vollbert/artix-dc-scm/Documentation/Pasted image 20260325133813.png

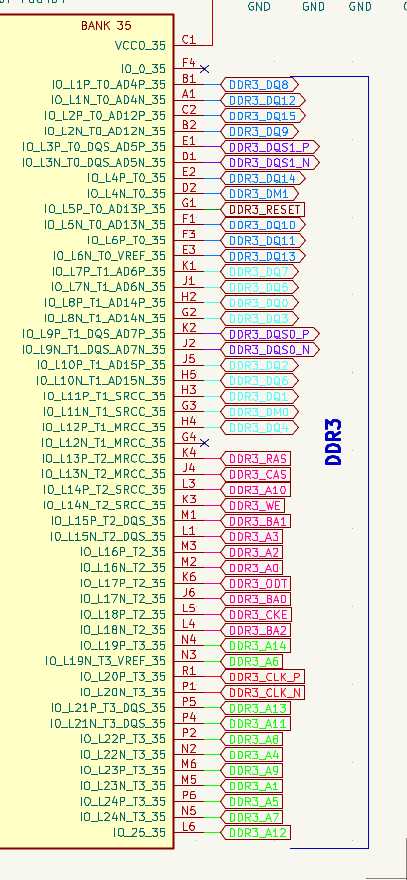
Documentation/Pasted image 20260325133813.png
