vollbert/artix-dc-scm/Documentation/Pasted image 20260326165011.png

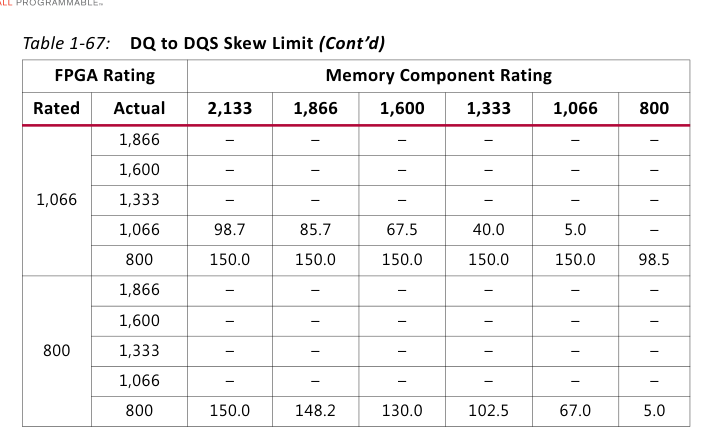
Documentation/Pasted image 20260326165011.png
