vollbert/artix-dc-scm/Documentation/Pasted image 20260402192206.png

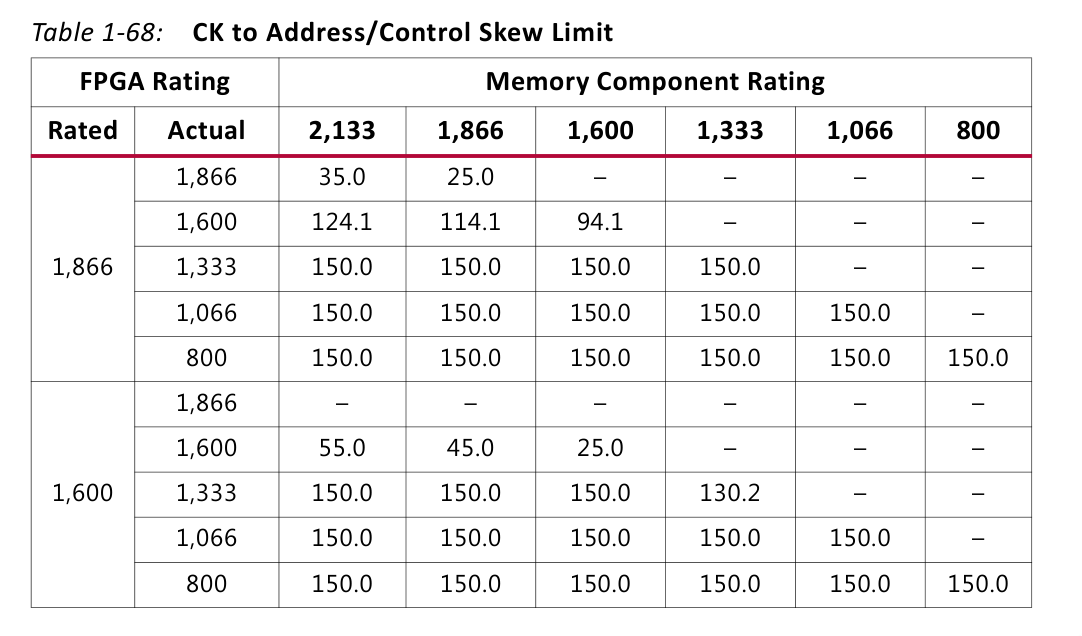
Documentation/Pasted image 20260402192206.png
