vollbert/artix-dc-scm/Documentation/Pasted image 20260403101223.png

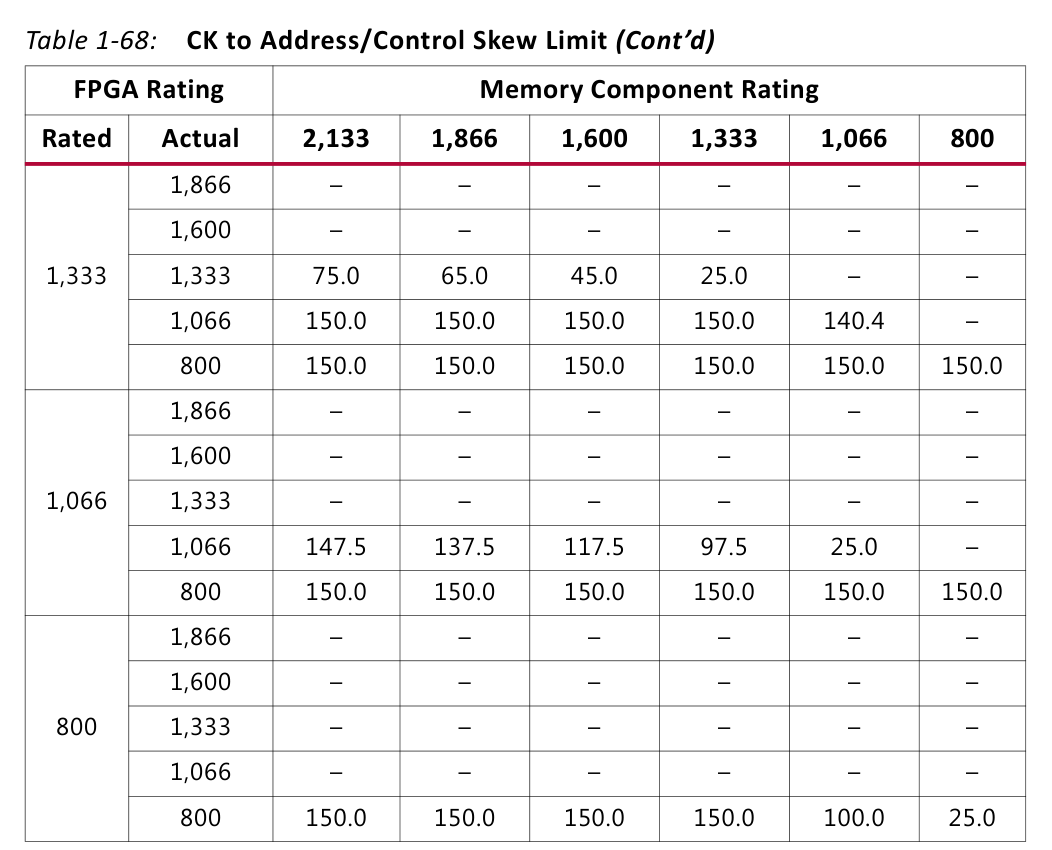
Documentation/Pasted image 20260403101223.png
