vollbert/artix-dc-scm/artix-dc-scm.kicad_sch

## KiCad design artix-dc-scm.kicad_sch (2026-04-19)

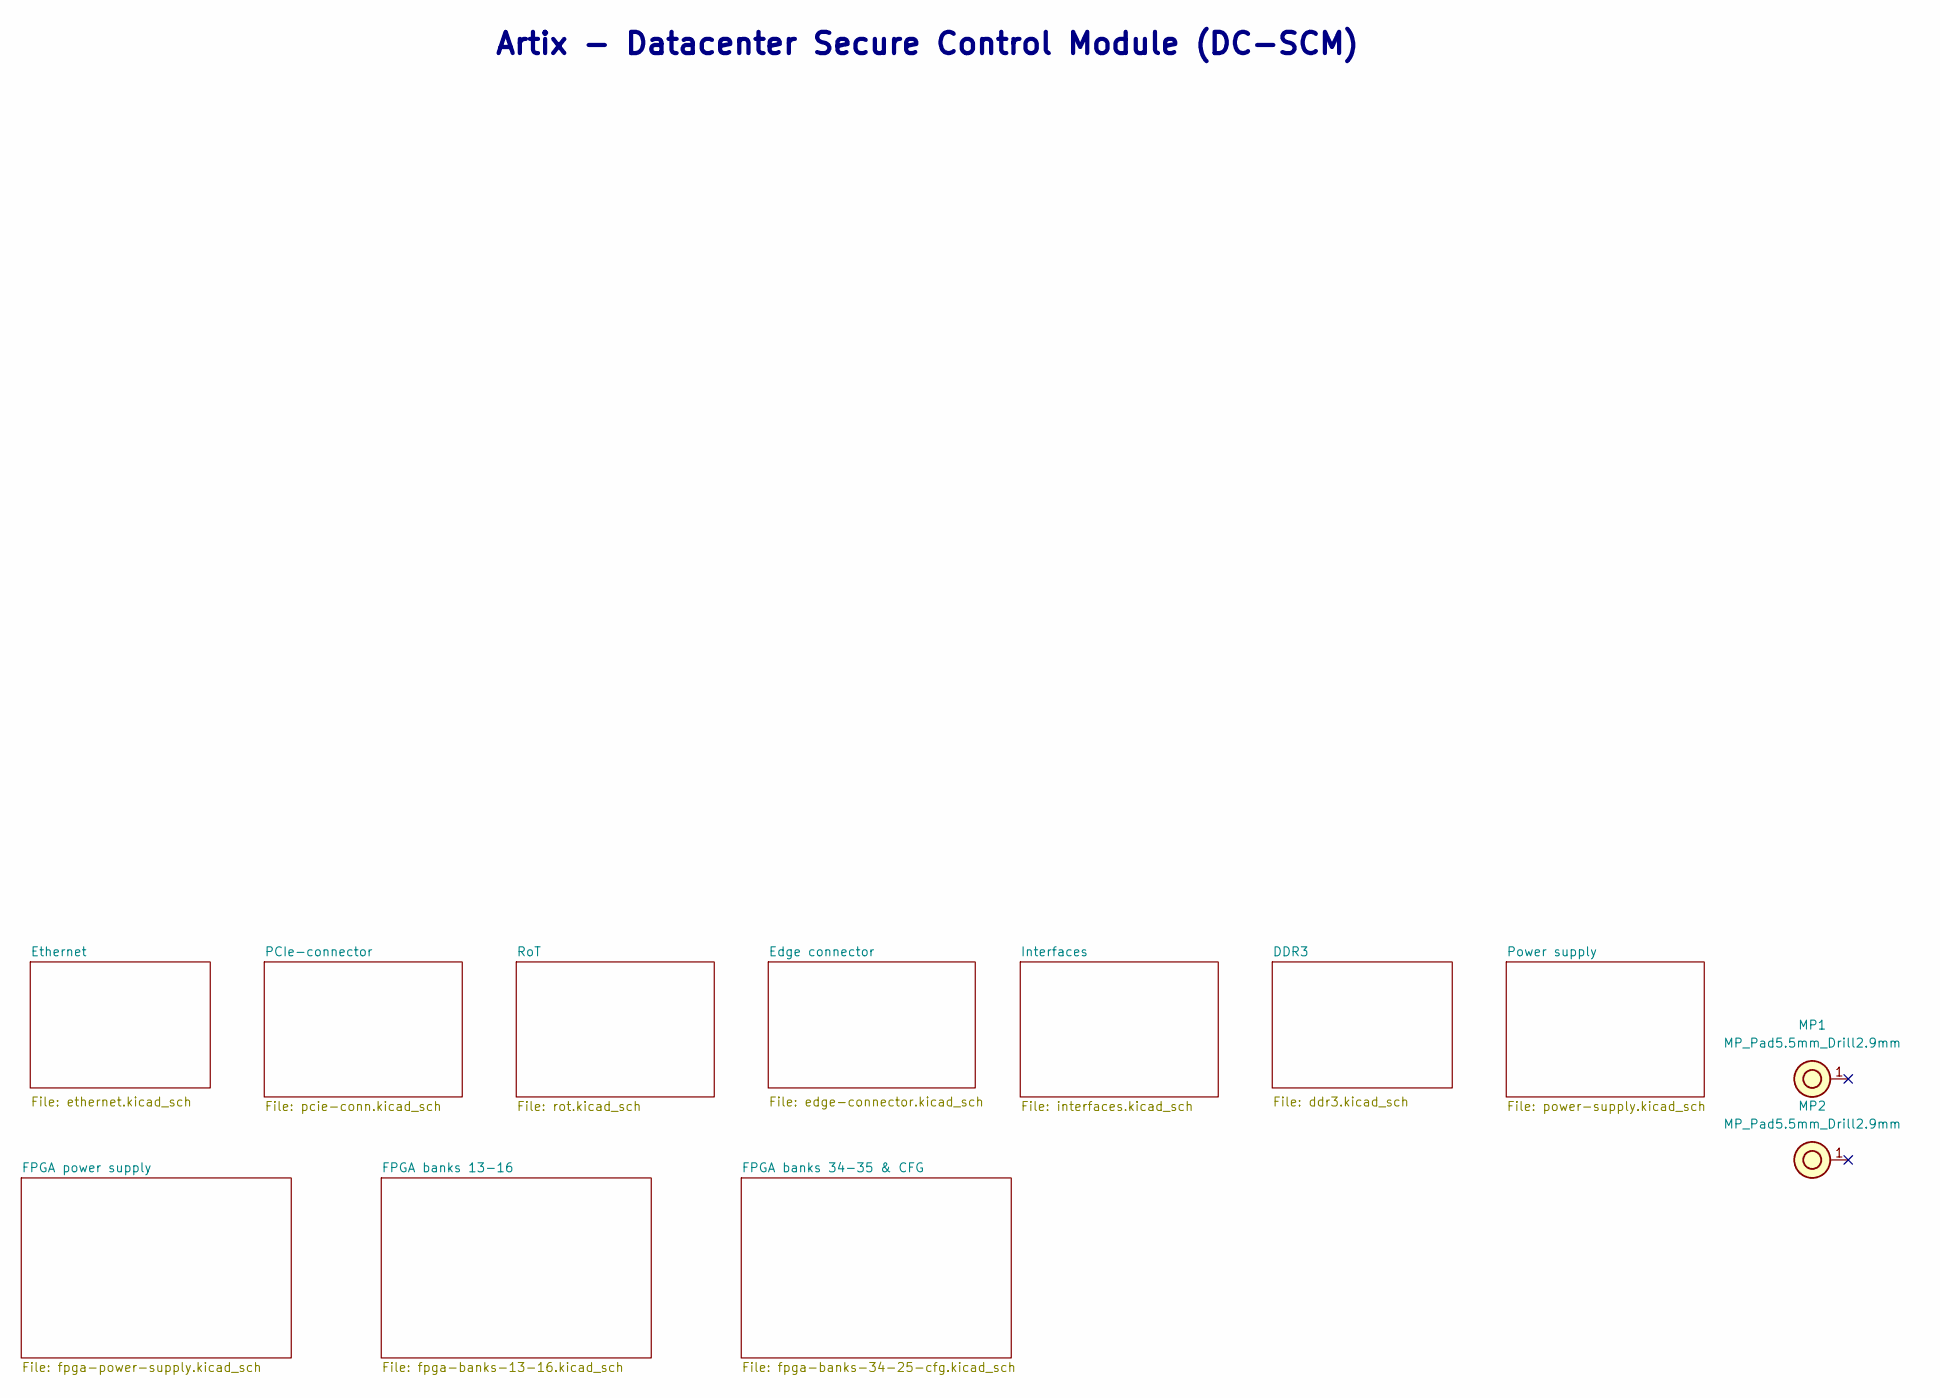
[picture p16: schematic artix-dc-scm.kicad_sch]

Parts:
MP1, MP2: MP_Pad5.5mm_Drill2.9mm

Notes on the sheet:
Artix - Datacenter Secure Control Module (DC-SCM)
