vollbert/artix-dc-scm/ddr3.kicad_sch

## KiCad design ddr3.kicad_sch (2026-04-19)

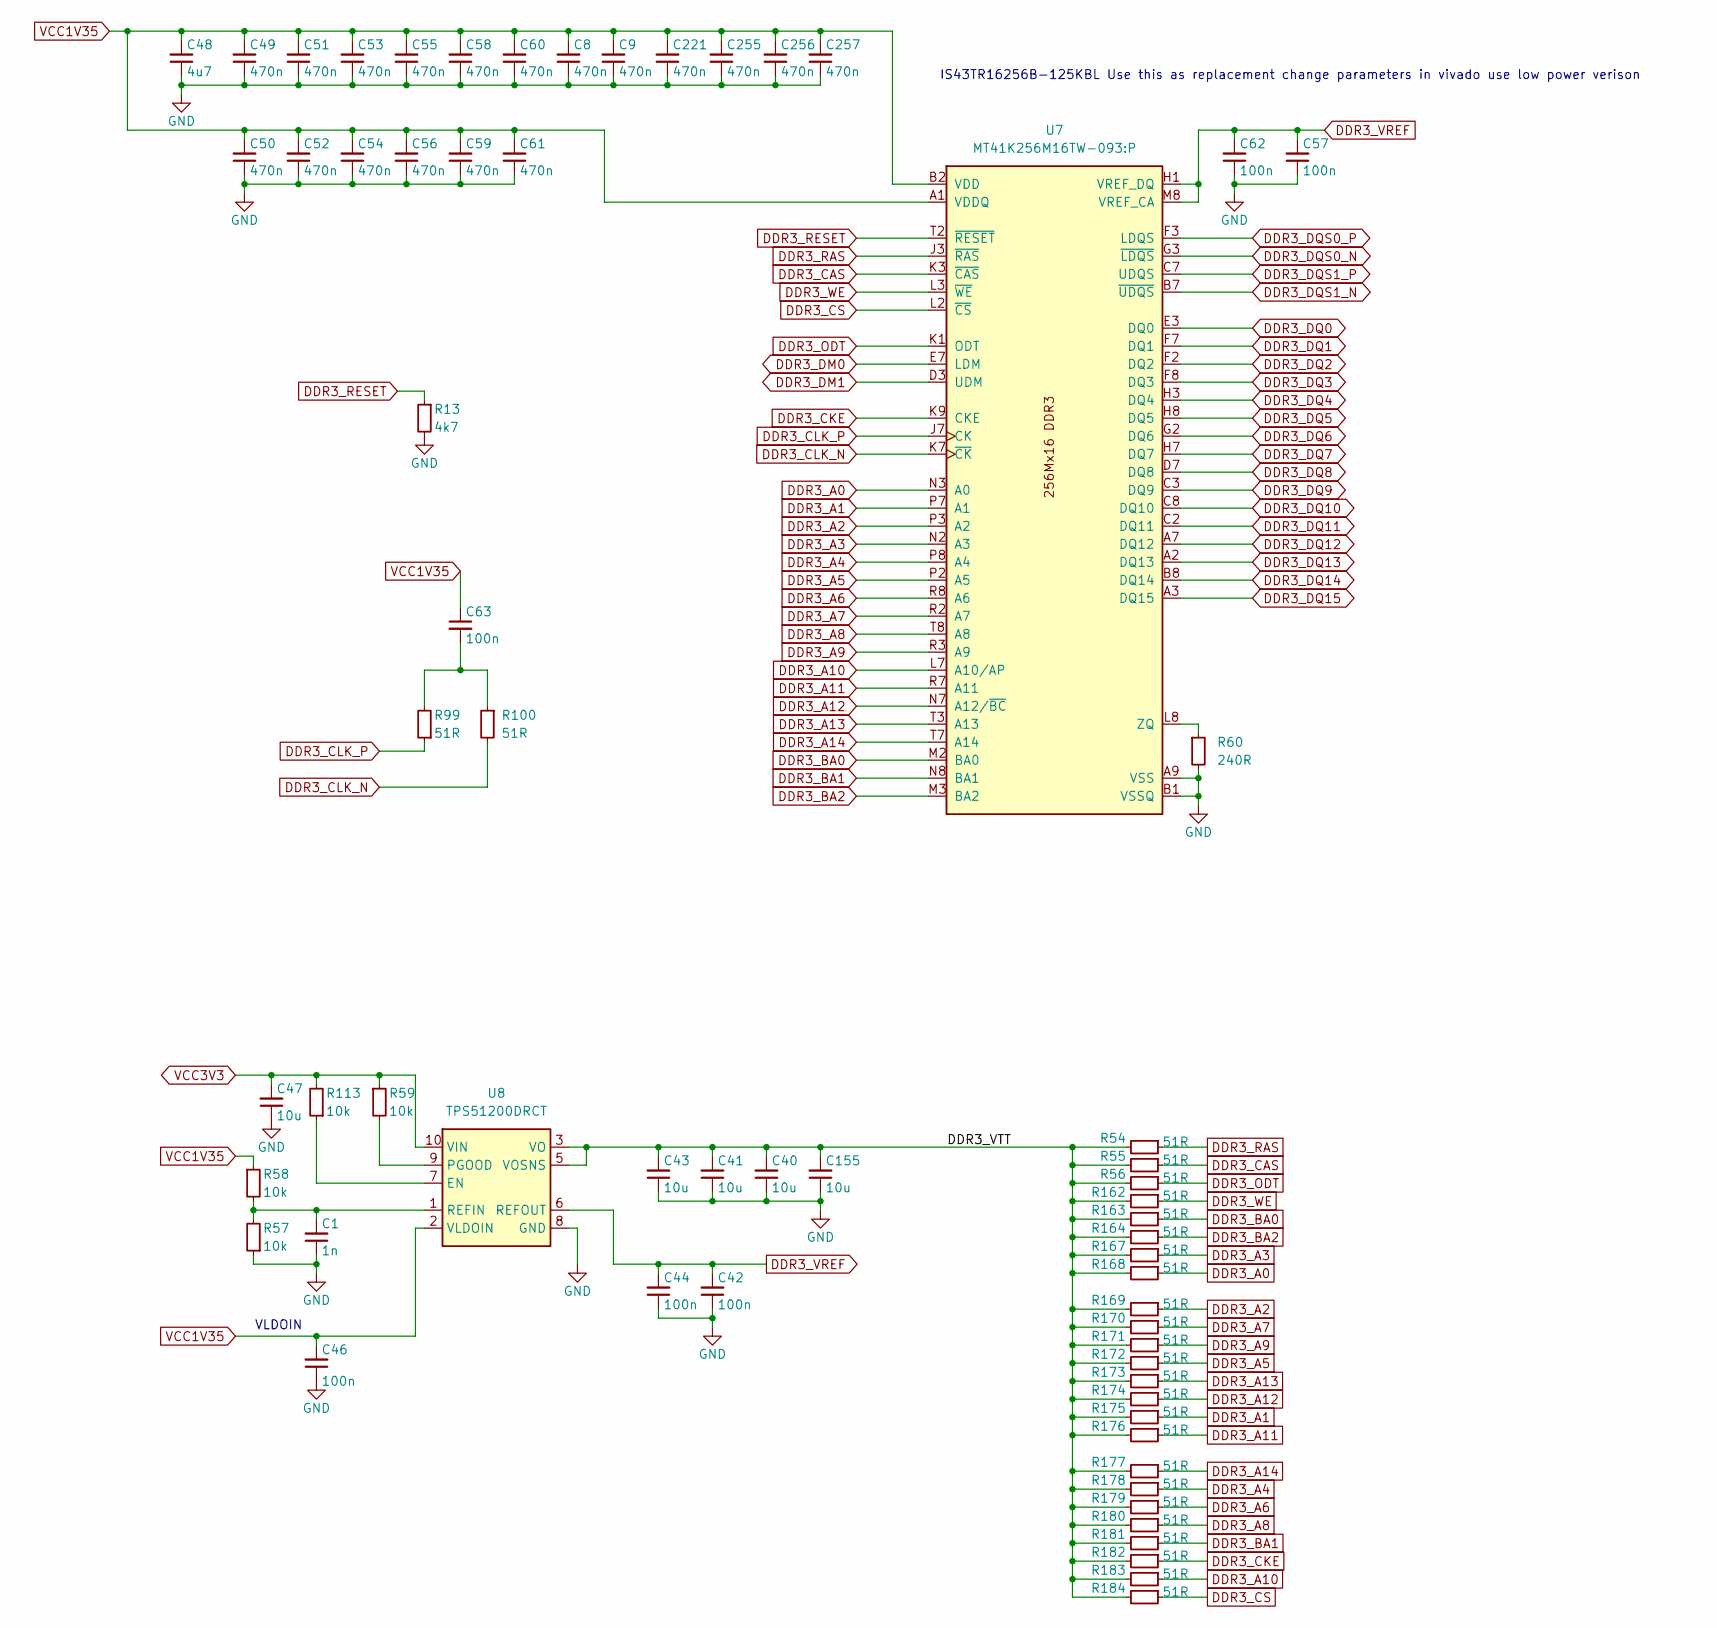
[picture p17: schematic ddr3.kicad_sch]

Parts:
C1: C_1n_0402; C_0402_1005Metric; Voltage 50V; MPN GRM1555C1H102JA01D
C8, C9, C49, C50, C51, C52, C53, C54, C55, C56, C58, C59, C60, C61, C221, C255, C256, C257: C_470n_0402; C_0402_1005Metric; MPN GXT155C80J474KE01D
C40, C41, C43, C47, C155: C_10u_0402; C_0402_1005Metric; MPN CC0402MRX5R5BB106
C42, C44, C46, C57, C62, C63: C_100n_6V3_0402; C_0402_1005Metric; MPN 0402X104K6R3CT
C48: C_4u7_0402; C_0402_1005Metric; MPN GRM155R61A475MEAAD
R13: R_4k7_0402; R_0402_1005Metric; Tolerance 1%; MPN RC0402FR-7D4K7L
R54, R55, R56, R99, R100, R162, R163, R164, R167, R168, R169, R170, R171, R172, R173, R174, R175, R176, R177, R178, R179, R180, R181, R182, R183, R184: R_51R_0402; R_0402_1005Metric; Tolerance 1%; MPN CR0402-FX-51R0GLF
R57, R58, R59, R113: R_10k_0402; R_0402_1005Metric; Tolerance 1%; MPN CR0402AFX-1002GAS
R60: R_240R_0402; R_0402_1005Metric; Tolerance 1%; MPN CR0402-FX-2400GLF
U7: MT41K256M16TW-093:P; BGA96C80P9X16_800X1400X120; MPN MT41K256M16TW-093:P
U8: TPS51200DRCT; VSON-10-1EP_3x3mm; MPN TPS51200DRCT

Connections:
DDR3_A0: R168.1, U7.N3 (A0)
DDR3_A1: R175.1, U7.P7 (A1)
DDR3_A2: R169.1, U7.P3 (A2)
DDR3_A3: R167.1, U7.N2 (A3)
DDR3_A4: R178.1, U7.P8 (A4)
DDR3_A5: R172.1, U7.P2 (A5)
DDR3_A6: R179.1, U7.R8 (A6)
DDR3_A7: R170.1, U7.R2 (A7)
DDR3_A8: R180.1, U7.T8 (A8)
DDR3_A9: R171.1, U7.R3 (A9)
DDR3_A10: R183.1, U7.L7 (A10/AP)
DDR3_A11: R176.1, U7.R7 (A11)
DDR3_A12: R174.1, U7.N7 (A12/~BC)
DDR3_A13: R173.1, U7.T3 (A13)
DDR3_A14: R177.1, U7.T7 (A14)
DDR3_BA0: R163.1, U7.M2 (BA0)
DDR3_BA1: R181.1, U7.N8 (BA1)
DDR3_BA2: R164.1, U7.M3 (BA2)
DDR3_CAS: R55.1, U7.K3 (~CAS)
DDR3_CKE: R182.1, U7.K9 (CKE)
DDR3_CLK_N: R100.2, U7.K7 (~CK)
DDR3_CLK_P: R99.1, U7.J7 (CK)
DDR3_CS: R184.1, U7.L2 (~CS)
DDR3_DM0: U7.E7 (LDM)
DDR3_DM1: U7.D3 (UDM)
DDR3_DQ0: U7.E3 (DQ0)
DDR3_DQ1: U7.F7 (DQ1)
DDR3_DQ2: U7.F2 (DQ2)
DDR3_DQ3: U7.F8 (DQ3)
DDR3_DQ4: U7.H3 (DQ4)
DDR3_DQ5: U7.H8 (DQ5)
DDR3_DQ6: U7.G2 (DQ6)
DDR3_DQ7: U7.H7 (DQ7)
DDR3_DQ8: U7.D7 (DQ8)
DDR3_DQ9: U7.C3 (DQ9)
DDR3_DQ10: U7.C8 (DQ10)
DDR3_DQ11: U7.C2 (DQ11)
DDR3_DQ12: U7.A7 (DQ12)
DDR3_DQ13: U7.A2 (DQ13)
DDR3_DQ14: U7.B8 (DQ14)
DDR3_DQ15: U7.A3 (DQ15)
DDR3_DQS0_N: U7.G3 (~LDQS)
DDR3_DQS0_P: U7.F3 (LDQS)
DDR3_DQS1_N: U7.B7 (~UDQS)
DDR3_DQS1_P: U7.C7 (UDQS)
DDR3_ODT: R56.1, U7.K1 (ODT)
DDR3_RAS: R54.1, U7.J3 (~RAS)
DDR3_RESET: R13.1, U7.T2 (~RESET)
DDR3_VREF: C42.2, C44.2, C57.2, C62.2, U7.H1 (VREF_DQ), U7.M8 (VREF_CA), U8.6 (REFOUT)
DDR3_VTT: C40.2, C41.2, C43.2, C155.2, R54.2, R55.2, R56.2, R162.2, R163.2, R164.2, R167.2, R168.2, R169.2, R170.2, R171.2, R172.2, R173.2, R174.2, R175.2, R176.2, R177.2, R178.2, R179.2, R180.2, R181.2, R182.2, R183.2, R184.2, U8.3 (VO), U8.5 (VOSNS)
DDR3_WE: R162.1, U7.L3 (~WE)
GND: C1.1, C8.1, C9.1, C40.1, C41.1, C42.1, C43.1, C44.1, C46.1, C47.1, C48.1, C49.1, C50.1, C51.1, C52.1, C53.1, C54.1, C55.1, C56.1, C57.1, C58.1, C59.1, C60.1, C61.1, C62.1, C155.1, C221.1, C255.1, C256.1, C257.1, R13.2, R57.1, R60.2, U7.A9 (VSS), U7.B1 (VSSQ), U7.B3 (VSS), U7.B9 (VSSQ), U7.D1 (VSSQ), U7.D8 (VSSQ), U7.E1 (VSS), U7.E2 (VSSQ), U7.E8 (VSSQ), U7.F9 (VSSQ), U7.G1 (VSSQ), U7.G8 (VSS), U7.G9 (VSSQ), U7.J2 (VSS), U7.J8 (VSS), U7.M1 (VSS), U7.M9 (VSS), U7.P1 (VSS), U7.P9 (VSS), U7.T1 (VSS), U7.T9 (VSS), U8.4 (GND), U8.8 (GND), U8.11 (GND)
unnamed: C1.2, R57.2, R58.2, U8.1 (REFIN)
unnamed: C63.2, R99.2, R100.1
unnamed: R59.2, U8.9 (PGOOD)
unnamed: R60.1, U7.L8 (ZQ)
unnamed: R113.1, U8.7 (EN)
unnamed: U7.J1 (NC), U7.J9 (NC), U7.L1 (NC), U7.L9 (NC), U7.M7 (NC)
VCC1V35: C8.2, C9.2, C46.2, C48.2, C49.2, C50.2, C51.2, C52.2, C53.2, C54.2, C55.2, C56.2, C58.2, C59.2, C60.2, C61.2, C63.1, C221.2, C255.2, C256.2, C257.2, R58.1, U7.A1 (VDDQ), U7.A8 (VDDQ), U7.B2 (VDD), U7.C1 (VDDQ), U7.C9 (VDDQ), U7.D2 (VDDQ), U7.D9 (VDD), U7.E9 (VDDQ), U7.F1 (VDDQ), U7.G7 (VDD), U7.H2 (VDDQ), U7.H9 (VDDQ), U7.K2 (VDD), U7.K8 (VDD), U7.N1 (VDD), U7.N9 (VDD), U7.R1 (VDD), U7.R9 (VDD), U8.2 (VLDOIN)
VCC3V3: C47.2, R59.1, R113.2, U8.10 (VIN)

Notes on the sheet:
VLDOIN
IS43TR16256B-125KBL Use this as replacement change parameters in vivado use low power verison
