vollbert/artix-dc-scm/edge-connector.kicad_sch

## KiCad design edge-connector.kicad_sch (2026-04-19)

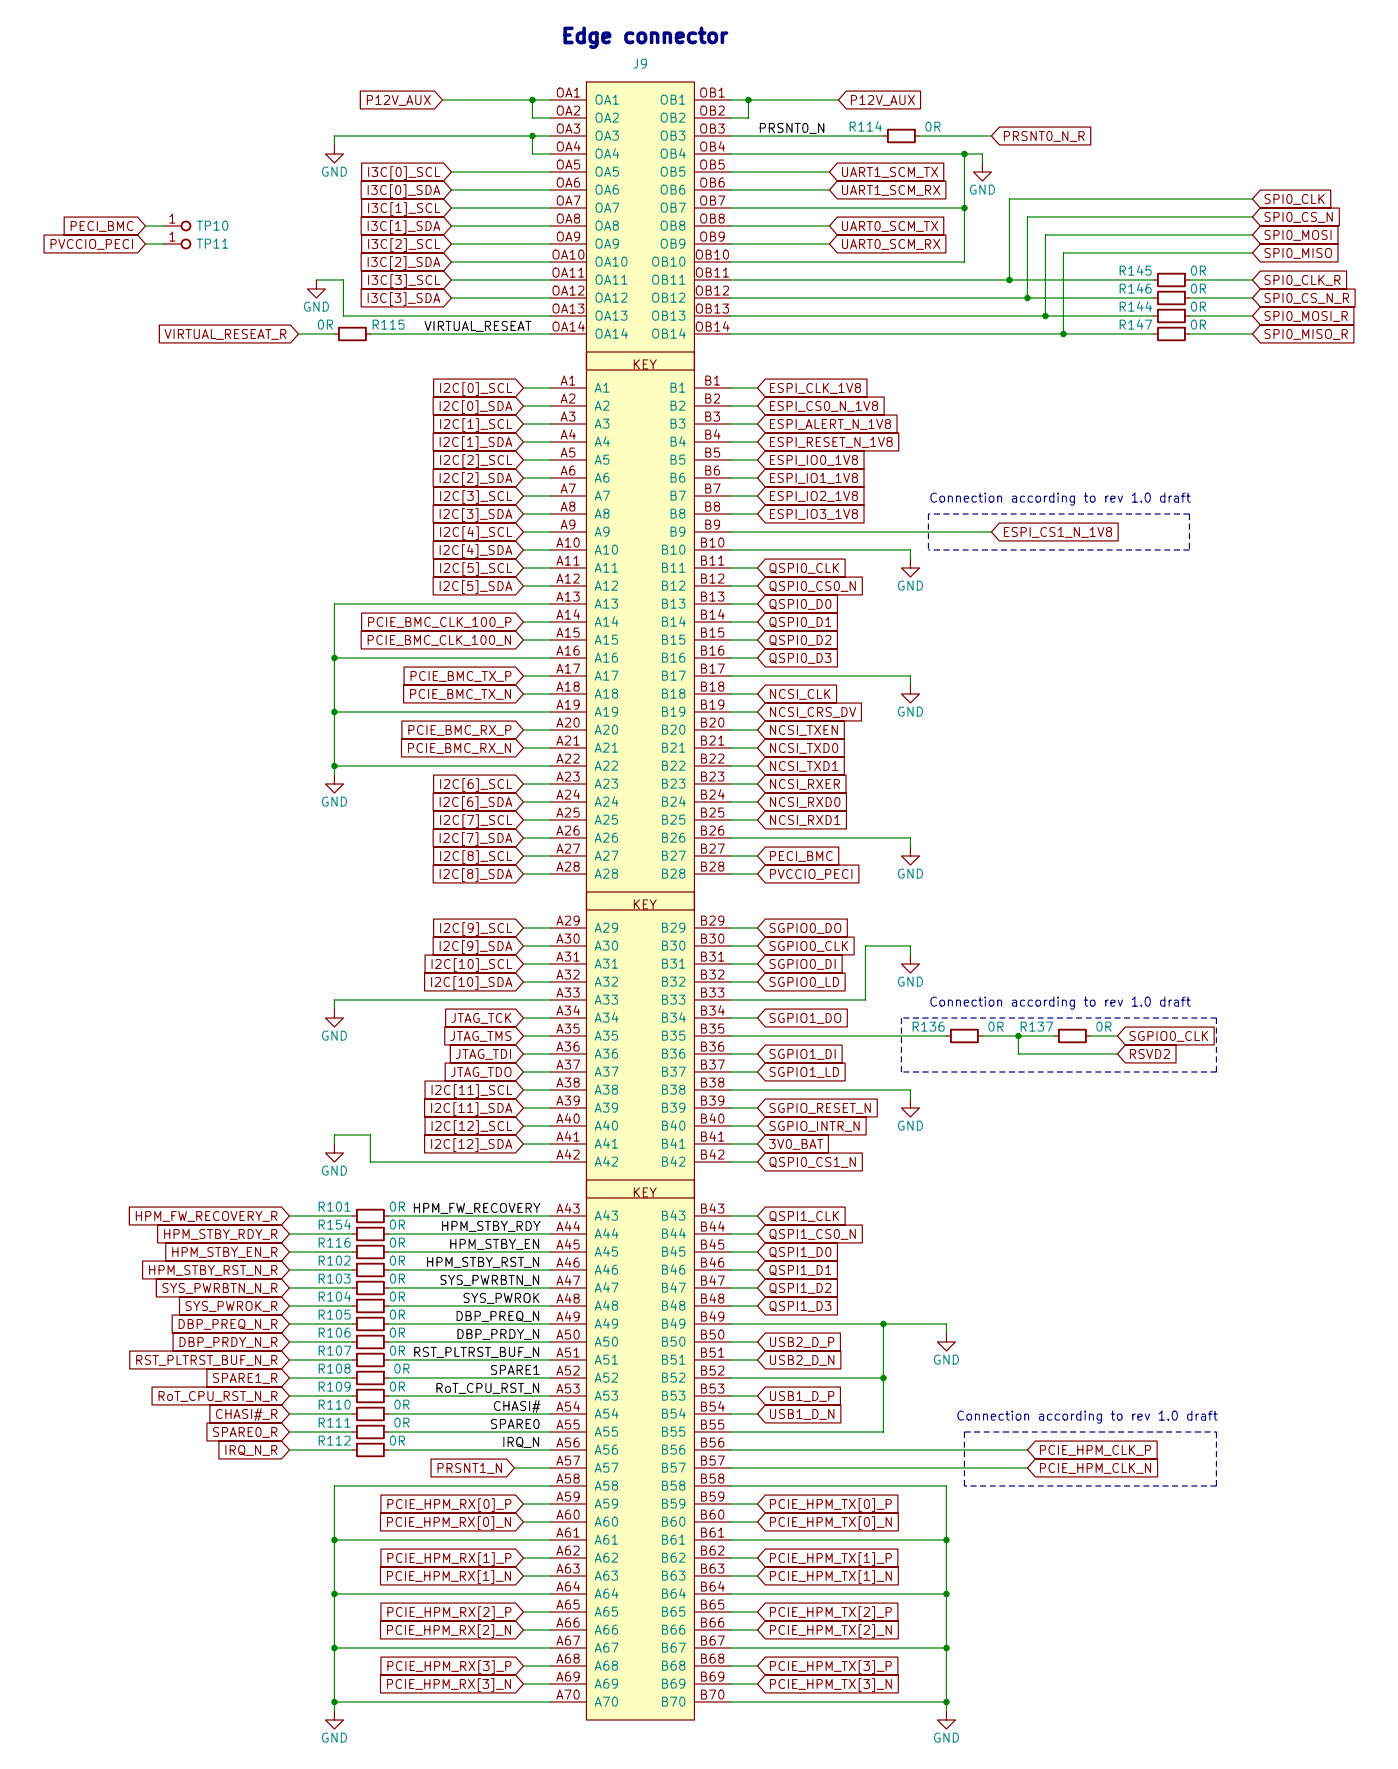
[picture p18: schematic edge-connector.kicad_sch]

Parts:
J9: SFF-TA-1002-4C+
R101, R102, R103, R104, R105, R106, R107, R108, R109, R110, R111, R112, R114, R115, R116, R136, R137, R144, R145, R146, R147, R154: R_0R_0402; R_0402_1005Metric; MPN RC0402JR-7D0RL
TP10, TP11: TP_1mm_SMD; TP_SMD_1mm

Connections:
3V0_BAT: J9.B41
CHASI#: J9.A54, R110.1
CHASI#_R: R110.2
DBP_PRDY_N: J9.A50, R106.2
DBP_PRDY_N_R: R106.1
DBP_PREQ_N: J9.A49, R105.2
DBP_PREQ_N_R: R105.1
ESPI_ALERT_N_1V8: J9.B3
ESPI_CLK_1V8: J9.B1
ESPI_CS0_N_1V8: J9.B2
ESPI_CS1_N_1V8: J9.B9
ESPI_IO0_1V8: J9.B5
ESPI_IO1_1V8: J9.B6
ESPI_IO2_1V8: J9.B7
ESPI_IO3_1V8: J9.B8
ESPI_RESET_N_1V8: J9.B4
GND: J9.A13, J9.A16, J9.A19, J9.A22, J9.A33, J9.A42, J9.A58, J9.A61, J9.A64, J9.A67, J9.A70, J9.B10, J9.B17, J9.B26, J9.B33, J9.B38, J9.B49, J9.B52, J9.B55, J9.B58, J9.B61, J9.B64, J9.B67, J9.B70, J9.OA3, J9.OA4, J9.OA13, J9.OB4, J9.OB7, J9.OB10
HPM_FW_RECOVERY: J9.A43, R101.2
HPM_FW_RECOVERY_R: R101.1
HPM_STBY_EN: J9.A45, R116.2
HPM_STBY_EN_R: R116.1
HPM_STBY_RDY: J9.A44, R154.2
HPM_STBY_RDY_R: R154.1
HPM_STBY_RST_N: J9.A46, R102.2
HPM_STBY_RST_N_R: R102.1
I2C[0]_SCL: J9.A1
I2C[0]_SDA: J9.A2
I2C[1]_SCL: J9.A3
I2C[1]_SDA: J9.A4
I2C[2]_SCL: J9.A5
I2C[2]_SDA: J9.A6
I2C[3]_SCL: J9.A7
I2C[3]_SDA: J9.A8
I2C[4]_SCL: J9.A9
I2C[4]_SDA: J9.A10
I2C[5]_SCL: J9.A11
I2C[5]_SDA: J9.A12
I2C[6]_SCL: J9.A23
I2C[6]_SDA: J9.A24
I2C[7]_SCL: J9.A25
I2C[7]_SDA: J9.A26
I2C[8]_SCL: J9.A27
I2C[8]_SDA: J9.A28
I2C[9]_SCL: J9.A29
I2C[9]_SDA: J9.A30
I2C[10]_SCL: J9.A31
I2C[10]_SDA: J9.A32
I2C[11]_SCL: J9.A38
I2C[11]_SDA: J9.A39
I2C[12]_SCL: J9.A40
I2C[12]_SDA: J9.A41
I3C[0]_SCL: J9.OA5
I3C[0]_SDA: J9.OA6
I3C[1]_SCL: J9.OA7
I3C[1]_SDA: J9.OA8
I3C[2]_SCL: J9.OA9
I3C[2]_SDA: J9.OA10
I3C[3]_SCL: J9.OA11
I3C[3]_SDA: J9.OA12
IRQ_N: J9.A56, R112.2
IRQ_N_R: R112.1
JTAG_TCK: J9.A34
JTAG_TDI: J9.A36
JTAG_TDO: J9.A37
JTAG_TMS: J9.A35
NCSI_CLK: J9.B18
NCSI_CRS_DV: J9.B19
NCSI_RXD0: J9.B24
NCSI_RXD1: J9.B25
NCSI_RXER: J9.B23
NCSI_TXD0: J9.B21
NCSI_TXD1: J9.B22
NCSI_TXEN: J9.B20
unnamed: J9.B35, R136.1
P12V_AUX: J9.OA1, J9.OA2, J9.OB1, J9.OB2
PCIE_BMC_CLK_100_N: J9.A15
PCIE_BMC_CLK_100_P: J9.A14
PCIE_BMC_RX_N: J9.A21
PCIE_BMC_RX_P: J9.A20
PCIE_BMC_TX_N: J9.A18
PCIE_BMC_TX_P: J9.A17
PCIE_HPM_CLK_N: J9.B57
PCIE_HPM_CLK_P: J9.B56
PCIE_HPM_RX[0]_N: J9.A60
PCIE_HPM_RX[0]_P: J9.A59
PCIE_HPM_RX[1]_N: J9.A63
PCIE_HPM_RX[1]_P: J9.A62
PCIE_HPM_RX[2]_N: J9.A66
PCIE_HPM_RX[2]_P: J9.A65
PCIE_HPM_RX[3]_N: J9.A69
PCIE_HPM_RX[3]_P: J9.A68
PCIE_HPM_TX[0]_N: J9.B60
PCIE_HPM_TX[0]_P: J9.B59
PCIE_HPM_TX[1]_N: J9.B63
PCIE_HPM_TX[1]_P: J9.B62
PCIE_HPM_TX[2]_N: J9.B66
PCIE_HPM_TX[2]_P: J9.B65
PCIE_HPM_TX[3]_N: J9.B69
PCIE_HPM_TX[3]_P: J9.B68
PECI_BMC: J9.B27, TP10.1
PRSNT0_N: J9.OB3, R114.2
PRSNT0_N_R: R114.1
PRSNT1_N: J9.A57
PVCCIO_PECI: J9.B28, TP11.1
QSPI0_CLK: J9.B11
QSPI0_CS0_N: J9.B12
QSPI0_CS1_N: J9.B42
QSPI0_D0: J9.B13
QSPI0_D1: J9.B14
QSPI0_D2: J9.B15
QSPI0_D3: J9.B16
QSPI1_CLK: J9.B43
QSPI1_CS0_N: J9.B44
QSPI1_D0: J9.B45
QSPI1_D1: J9.B46
QSPI1_D2: J9.B47
QSPI1_D3: J9.B48
RST_PLTRST_BUF_N: J9.A51, R107.2
RST_PLTRST_BUF_N_R: R107.1
RSVD2: R136.2, R137.1
RoT_CPU_RST_N: J9.A53, R109.2
RoT_CPU_RST_N_R: R109.1
SGPIO0_CLK: J9.B30, R137.2
SGPIO0_DI: J9.B31
SGPIO0_DO: J9.B29
SGPIO0_LD: J9.B32
SGPIO1_DI: J9.B36
SGPIO1_DO: J9.B34
SGPIO1_LD: J9.B37
SGPIO_INTR_N: J9.B40
SGPIO_RESET_N: J9.B39
SPARE0: J9.A55, R111.1
SPARE0_R: R111.2
SPARE1: J9.A52, R108.1
SPARE1_R: R108.2
SPI0_CLK: J9.OB11, R145.2
SPI0_CLK_R: R145.1
SPI0_CS_N: J9.OB12, R146.2
SPI0_CS_N_R: R146.1
SPI0_MISO: J9.OB14, R147.2
SPI0_MISO_R: R147.1
SPI0_MOSI: J9.OB13, R144.2
SPI0_MOSI_R: R144.1
SYS_PWRBTN_N: J9.A47, R103.2
SYS_PWRBTN_N_R: R103.1
SYS_PWROK: J9.A48, R104.2
SYS_PWROK_R: R104.1
UART0_SCM_RX: J9.OB9
UART0_SCM_TX: J9.OB8
UART1_SCM_RX: J9.OB6
UART1_SCM_TX: J9.OB5
USB1_D_N: J9.B54
USB1_D_P: J9.B53
USB2_D_N: J9.B51
USB2_D_P: J9.B50
VIRTUAL_RESEAT: J9.OA14, R115.2
VIRTUAL_RESEAT_R: R115.1

Notes on the sheet:
Edge connector
Connection according to rev 1.0 draft
