vollbert/artix-dc-scm/ethernet.kicad_sch

## KiCad design ethernet.kicad_sch (2026-04-19)

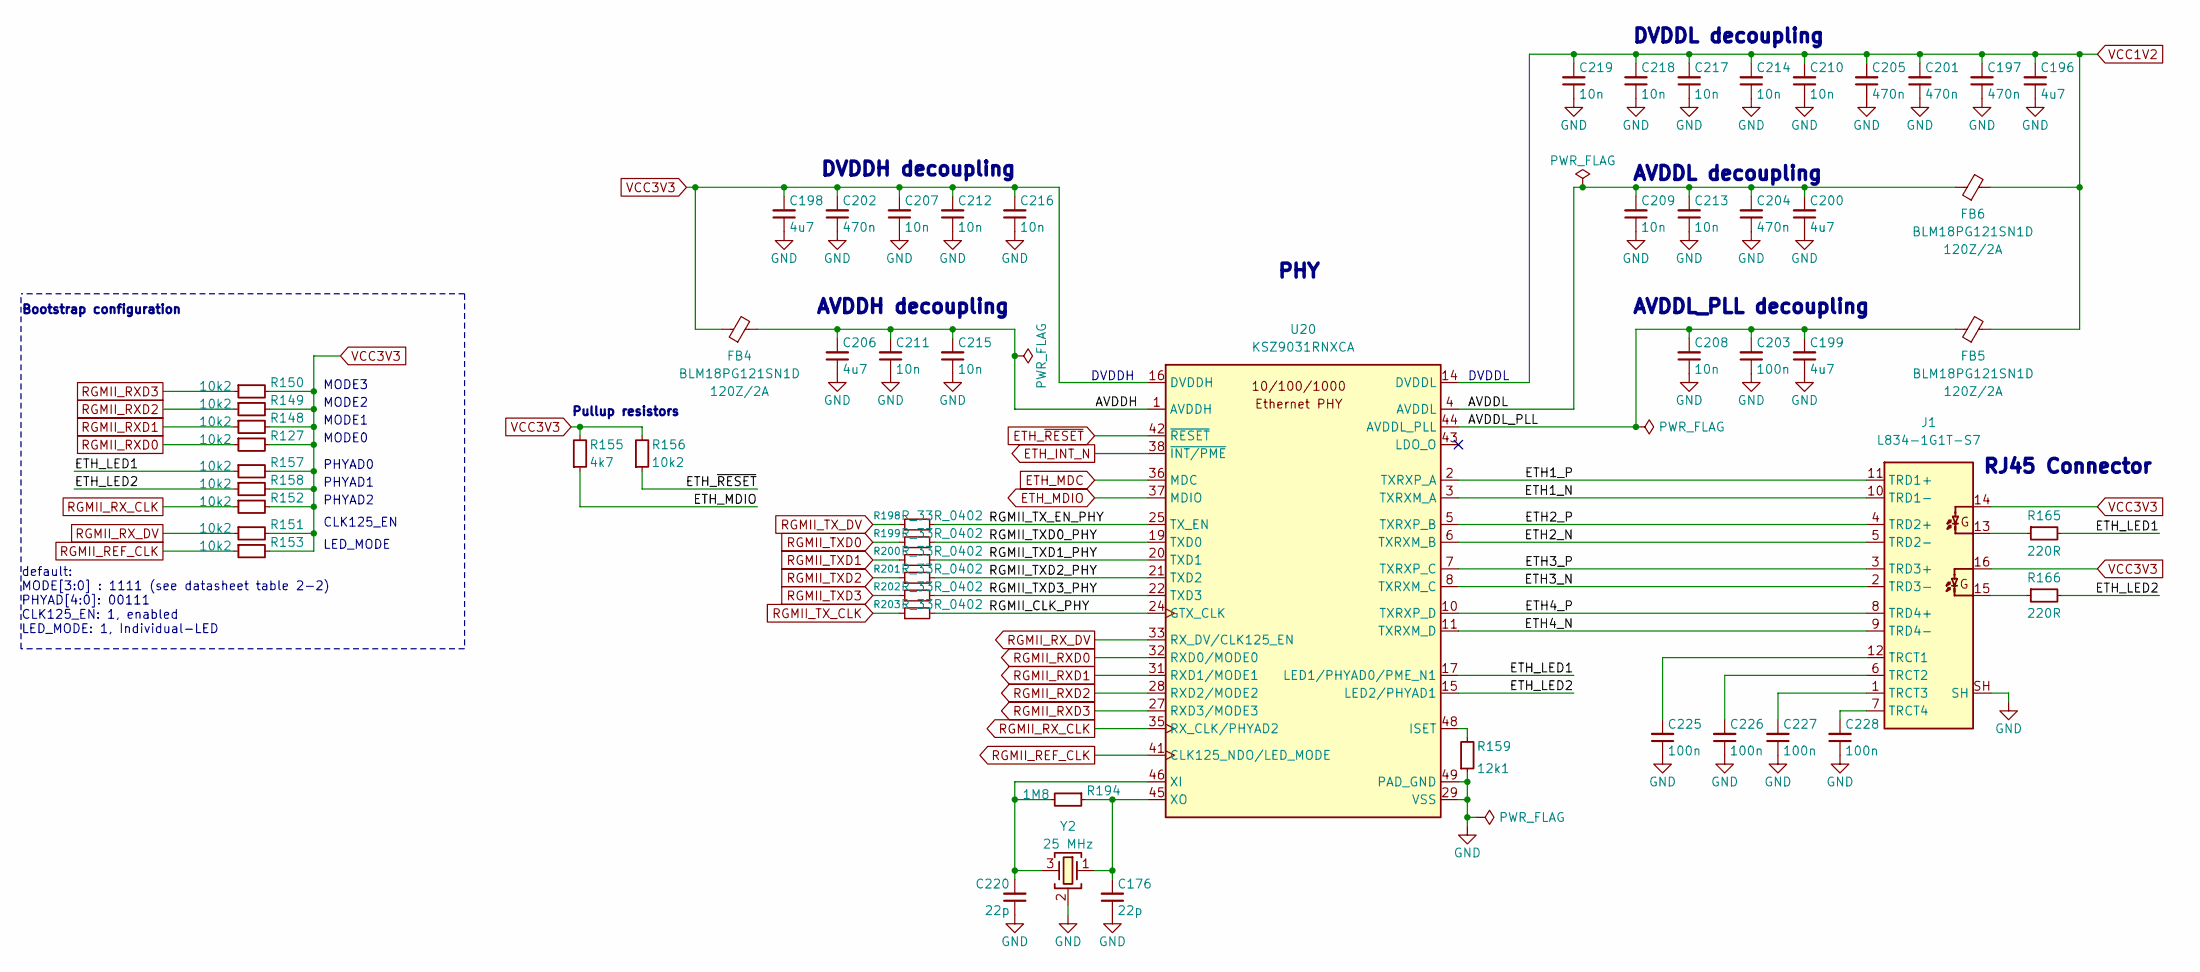
[picture p19: schematic ethernet.kicad_sch]

Parts:
C176, C220: C_22p_0402; C_0402_1005Metric; MPN CC0402JRNPO9BN220
C196, C198, C199, C200, C206: C_4u7_0402; C_0402_1005Metric; MPN GRM155R61A475MEAAD
C197, C201, C202, C204, C205: C_470n_0402; C_0402_1005Metric; MPN GXT155C80J474KE01D
C203, C225, C226, C227, C228: C_100n_0402; C_0402_1005Metric; Voltage 50V; MPN GRM155R61H104KE14D
C207, C208, C209, C210, C211, C212, C213, C214, C215, C216, C217, C218, C219: C_10n_0402; C_0402_1005Metric; Voltage 50V; MPN GRM155R71H103KA88D
FB4, FB5, FB6: FB_120Z_2A_Murata-BLM18PG_0603; FB_0603_1608Metric; MPN BLM18PG121SN1D
J1: L834-1G1T-S7; RJ45_BEL_L834-1G1T-S7; MPN L834-1G1T-S7
R127, R148, R149, R150, R151, R152, R153, R156, R157, R158: R_10k2_0402; R_0402_1005Metric; Tolerance 1%; MPN CR0402-FX-1022GLF
R155: R_4k7_0402; R_0402_1005Metric; Tolerance 1%; MPN RC0402FR-7D4K7L
R159: R_12k1_0402; R_0402_1005Metric; Tolerance 1%; MPN CR0402-FX-1212GLF
R165, R166: R_220R_0402; R_0402_1005Metric; Tolerance 1%; MPN CR0402-FX-2200GLF
R194: R_1M8_0402; R_0402_1005Metric; Tolerance 1%; MPN RC0402FR-131M8L
R198, R199, R200, R201, R202, R203: R_33R_0402; R_0402_1005Metric; MPN MCS04020C3309FE000
U20: KSZ9031RNXCA; QFN-48-1EP_7x7x0.9mm_P0.5mm_EP3.5x3.5mm; MPN KSZ9031RNXCA
Y2: Resonator_25MHz_ABM8G; Resonator_SMD_Abracon_ABM8G_3.2x2.5mm; MPN ABM8G-25.000MHZ-18-D2Y-T3

Connections:
AVDDH: C206.2, C211.2, C215.2, FB4.2, U20.1 (AVDDH), U20.12 (AVDDH)
AVDDL: C200.2, C204.2, C209.2, C213.2, FB6.1, U20.4 (AVDDL), U20.9 (AVDDL)
AVDDL_PLL: C199.2, C203.2, C208.2, FB5.1, U20.44 (AVDDL_PLL)
ETH1_N: J1.10 (TRD1-), U20.3 (TXRXM_A)
ETH1_P: J1.11 (TRD1+), U20.2 (TXRXP_A)
ETH2_N: J1.5 (TRD2-), U20.6 (TXRXM_B)
ETH2_P: J1.4 (TRD2+), U20.5 (TXRXP_B)
ETH3_N: J1.2 (TRD3-), U20.8 (TXRXM_C)
ETH3_P: J1.3 (TRD3+), U20.7 (TXRXP_C)
ETH4_N: J1.9 (TRD4-), U20.11 (TXRXM_D)
ETH4_P: J1.8 (TRD4+), U20.10 (TXRXP_D)
ETH_INT_N: U20.38 (~INT/PME)
ETH_LED1: R157.1, R165.2, U20.17 (LED1/PHYAD0/PME_N1)
ETH_LED2: R158.1, R166.2, U20.15 (LED2/PHYAD1)
ETH_MDC: U20.36 (MDC)
ETH_MDIO: R155.1, U20.37 (MDIO)
ETH_~RESET: R156.1, U20.42 (~RESET)
GND: C176.1, C196.1, C197.1, C198.1, C199.1, C200.1, C201.1, C202.1, C203.1, C204.1, C205.1, C206.1, C207.1, C208.1, C209.1, C210.1, C211.1, C212.1, C213.1, C214.1, C215.1, C216.1, C217.1, C218.1, C219.1, C220.1, C225.1, C226.1, C227.1, C228.1, J1.SH, R159.1, U20.29 (VSS), U20.49 (PAD_GND), Y2.2 (SH), Y2.4 (SH)
unnamed: C176.2, R194.1, U20.45 (XO), Y2.1
unnamed: C220.2, R194.2, U20.46 (XI), Y2.3
unnamed: C225.2, J1.12 (TRCT1)
unnamed: C226.2, J1.6 (TRCT2)
unnamed: C227.2, J1.1 (TRCT3)
unnamed: C228.2, J1.7 (TRCT4)
unnamed: J1.13, R165.1
unnamed: J1.15, R166.1
unnamed: R159.2, U20.48 (ISET)
RGMII_CLK_PHY: R203.2, U20.24 (GTX_CLK)
RGMII_REF_CLK: R153.1, U20.41 (CLK125_NDO/LED_MODE)
RGMII_RXD0: R127.1, U20.32 (RXD0/MODE0)
RGMII_RXD1: R148.1, U20.31 (RXD1/MODE1)
RGMII_RXD2: R149.1, U20.28 (RXD2/MODE2)
RGMII_RXD3: R150.1, U20.27 (RXD3/MODE3)
RGMII_RX_CLK: R152.1, U20.35 (RX_CLK/PHYAD2)
RGMII_RX_DV: R151.1, U20.33 (RX_DV/CLK125_EN)
RGMII_TXD0: R199.1
RGMII_TXD0_PHY: R199.2, U20.19 (TXD0)
RGMII_TXD1: R200.1
RGMII_TXD1_PHY: R200.2, U20.20 (TXD1)
RGMII_TXD2: R201.1
RGMII_TXD2_PHY: R201.2, U20.21 (TXD2)
RGMII_TXD3: R202.1
RGMII_TXD3_PHY: R202.2, U20.22 (TXD3)
RGMII_TX_CLK: R203.1
RGMII_TX_DV: R198.1
RGMII_TX_EN_PHY: R198.2, U20.25 (TX_EN)
VCC1V2: C196.2, C197.2, C201.2, C205.2, C210.2, C214.2, C217.2, C218.2, C219.2, FB5.2, FB6.2, U20.14 (DVDDL), U20.18 (DVDDL), U20.23 (DVDDL), U20.26 (DVDDL), U20.30 (DVDDL), U20.39 (DVDDL)
VCC3V3: C198.2, C202.2, C207.2, C212.2, C216.2, FB4.1, J1.14, J1.16, R127.2, R148.2, R149.2, R150.2, R151.2, R152.2, R153.2, R155.2, R156.2, R157.2, R158.2, U20.16 (DVDDH), U20.34 (DVDDH), U20.40 (DVDDH)

Notes on the sheet:
DVDDL decoupling
DVDDL
MODE0
PHY
MODE1
default: MODE[3:0] : 1111 (see datasheet table 2-2) PHYAD[4:0]: 00111 CLK125_EN: 1, enabled LED_MODE: 1, Individual-LED
AVDDL_PLL decoupling
MODE3
MODE2
PHYAD1
PHYAD2
AVDDH decoupling
DVDDH
CLK125_EN
AVDDL decoupling
LED_MODE
Pullup resistors
Bootstrap configuration
DVDDH decoupling
RJ45 Connector
PHYAD0
