vollbert/artix-dc-scm/fpga-banks-13-16.kicad_sch

## KiCad design fpga-banks-13-16.kicad_sch (2026-04-19)

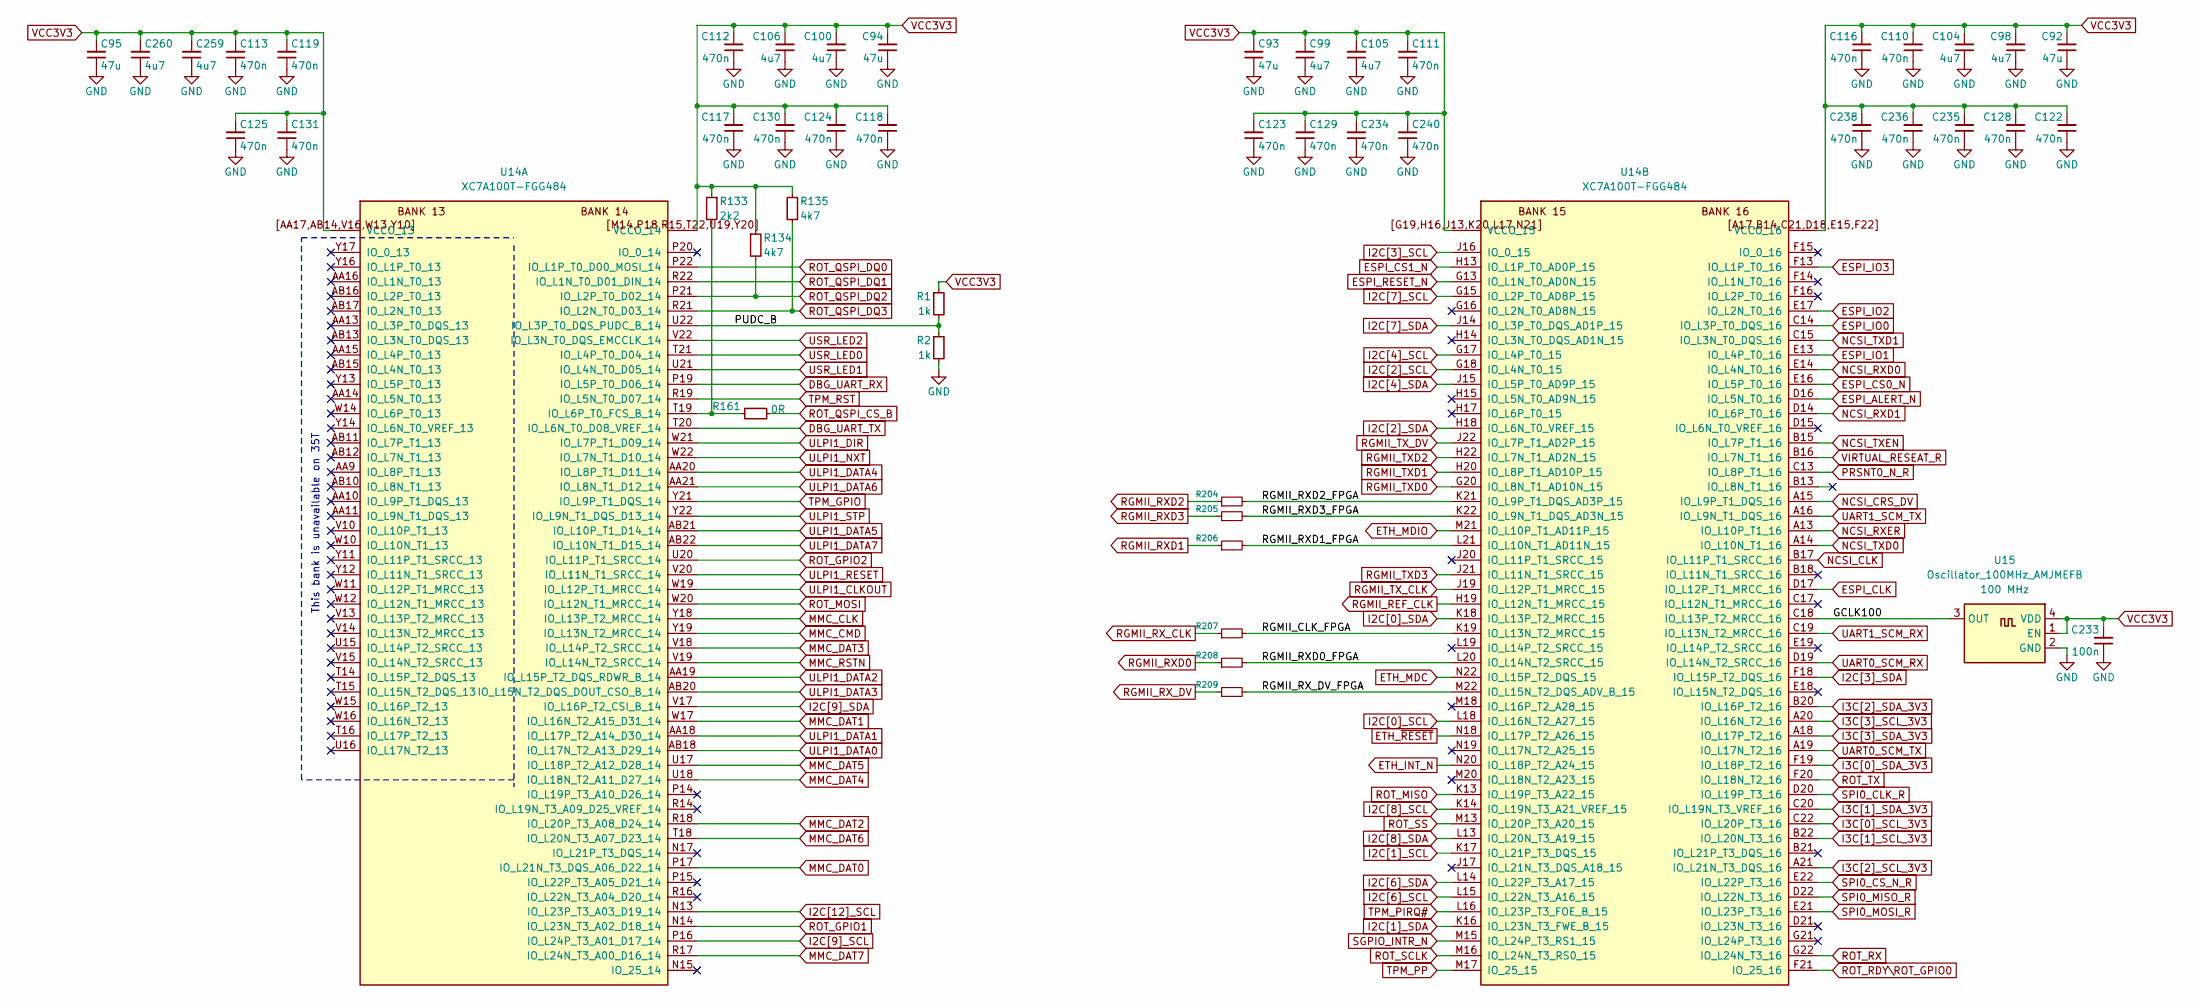
[picture p20: schematic fpga-banks-13-16.kicad_sch]

Parts:
C92, C93, C94, C95: C_47u_1210; C_1210_3225Metric; MPN C1210C476K8RAC7210
C98, C99, C100, C104, C105, C106, C259, C260: C_4u7_0603; C_0603_1608Metric; MPN C0603C475K9PAC
C110, C111, C112, C113, C116, C117, C118, C119, C122, C123, C124, C125, C128, C129, C130, C131, C234, C235, C236, C238, C240: C_470n_0402; C_0402_1005Metric; MPN GXT155C80J474KE01D
C233: C_100n_0402; C_0402_1005Metric; Voltage 50V; MPN GRM155R61H104KE14D
R1, R2: R_1k_0402; R_0402_1005Metric; Tolerance 1%; MPN CR0402-FX-1001GLF
R133: R_2k2_0402; R_0402_1005Metric; Tolerance 1%; MPN AC0402FR-7D2K2L
R134, R135: R_4k7_0402; R_0402_1005Metric; Tolerance 1%; MPN RC0402FR-7D4K7L
R161: R_0R_0402; R_0402_1005Metric; MPN RC0402JR-7D0RL
R204, R205, R206, R207, R208, R209: R_33R_0402; R_0402_1005Metric; MPN MCS04020C3309FE000
U14: XC7A100T-FGG484; BGA-484_23x23mm_Layout22x22_P1mm_FGG484; MPN XC7A100T-2FGG484C
U15: Oscillator_100MHz_AMJMEFB; Oscillator_SMD_Abracon_AMJM_3.2x2.5mm; MPN ASEMB-100.000MHZ-XY-T

Connections:
DBG_UART_RX: U14.P19 (IO_L5P_T0_D06_14)
DBG_UART_TX: U14.T20 (IO_L6N_T0_D08_VREF_14)
ESPI_ALERT_N: U14.D16 (IO_L5N_T0_16)
ESPI_CLK: U14.D17 (IO_L12P_T1_MRCC_16)
ESPI_CS0_N: U14.E16 (IO_L5P_T0_16)
ESPI_CS1_N: U14.H13 (IO_L1P_T0_AD0P_15)
ESPI_IO0: U14.C14 (IO_L3P_T0_DQS_16)
ESPI_IO1: U14.E13 (IO_L4P_T0_16)
ESPI_IO2: U14.E17 (IO_L2N_T0_16)
ESPI_IO3: U14.F13 (IO_L1P_T0_16)
ESPI_RESET_N: U14.G13 (IO_L1N_T0_AD0N_15)
ETH_INT_N: U14.N20 (IO_L18P_T2_A24_15)
ETH_MDC: U14.N22 (IO_L15P_T2_DQS_15)
ETH_MDIO: U14.M21 (IO_L10P_T1_AD11P_15)
ETH_~RESET: U14.N18 (IO_L17P_T2_A26_15)
GCLK100: U14.C18 (IO_L13P_T2_MRCC_16), U15.3 (OUT)
GND: C92.1, C93.1, C94.1, C95.1, C98.1, C99.1, C100.1, C104.1, C105.1, C106.1, C110.1, C111.1, C112.1, C113.1, C116.1, C117.1, C118.1, C119.1, C122.1, C123.1, C124.1, C125.1, C128.1, C129.1, C130.1, C131.1, C233.1, C234.1, C235.1, C236.1, C238.1, C240.1, C259.1, C260.1, R2.2, U15.2 (GND)
I2C[0]_SCL: U14.L18 (IO_L16N_T2_A27_15)
I2C[0]_SDA: U14.K18 (IO_L13P_T2_MRCC_15)
I2C[1]_SCL: U14.K17 (IO_L21P_T3_DQS_15)
I2C[1]_SDA: U14.K16 (IO_L23N_T3_FWE_B_15)
I2C[2]_SCL: U14.G18 (IO_L4N_T0_15)
I2C[2]_SDA: U14.H18 (IO_L6N_T0_VREF_15)
I2C[3]_SCL: U14.J16 (IO_0_15)
I2C[3]_SDA: U14.F18 (IO_L15P_T2_DQS_16)
I2C[4]_SCL: U14.G17 (IO_L4P_T0_15)
I2C[4]_SDA: U14.J15 (IO_L5P_T0_AD9P_15)
I2C[6]_SCL: U14.L15 (IO_L22N_T3_A16_15)
I2C[6]_SDA: U14.L14 (IO_L22P_T3_A17_15)
I2C[7]_SCL: U14.G15 (IO_L2P_T0_AD8P_15)
I2C[7]_SDA: U14.J14 (IO_L3P_T0_DQS_AD1P_15)
I2C[8]_SCL: U14.K14 (IO_L19N_T3_A21_VREF_15)
I2C[8]_SDA: U14.L13 (IO_L20N_T3_A19_15)
I2C[9]_SCL: U14.P16 (IO_L24P_T3_A01_D17_14)
I2C[9]_SDA: U14.V17 (IO_L16P_T2_CSI_B_14)
I2C[12]_SCL: U14.N13 (IO_L23P_T3_A03_D19_14)
I3C[0]_SCL_3V3: U14.C22 (IO_L20P_T3_16)
I3C[0]_SDA_3V3: U14.F19 (IO_L18P_T2_16)
I3C[1]_SCL_3V3: U14.B22 (IO_L20N_T3_16)
I3C[1]_SDA_3V3: U14.C20 (IO_L19N_T3_VREF_16)
I3C[2]_SCL_3V3: U14.A21 (IO_L21N_T3_DQS_16)
I3C[2]_SDA_3V3: U14.B20 (IO_L16P_T2_16)
I3C[3]_SCL_3V3: U14.A20 (IO_L16N_T2_16)
I3C[3]_SDA_3V3: U14.A18 (IO_L17P_T2_16)
MMC_CLK: U14.Y18 (IO_L13P_T2_MRCC_14)
MMC_CMD: U14.Y19 (IO_L13N_T2_MRCC_14)
MMC_DAT0: U14.P17 (IO_L21N_T3_DQS_A06_D22_14)
MMC_DAT1: U14.W17 (IO_L16N_T2_A15_D31_14)
MMC_DAT2: U14.R18 (IO_L20P_T3_A08_D24_14)
MMC_DAT3: U14.V18 (IO_L14P_T2_SRCC_14)
MMC_DAT4: U14.U18 (IO_L18N_T2_A11_D27_14)
MMC_DAT5: U14.U17 (IO_L18P_T2_A12_D28_14)
MMC_DAT6: U14.T18 (IO_L20N_T3_A07_D23_14)
MMC_DAT7: U14.R17 (IO_L24N_T3_A00_D16_14)
MMC_RSTN: U14.V19 (IO_L14N_T2_SRCC_14)
NCSI_CLK: U14.B17 (IO_L11P_T1_SRCC_16)
NCSI_CRS_DV: U14.A15 (IO_L9P_T1_DQS_16)
NCSI_RXD0: U14.E14 (IO_L4N_T0_16)
NCSI_RXD1: U14.D14 (IO_L6P_T0_16)
NCSI_RXER: U14.A13 (IO_L10P_T1_16)
NCSI_TXD0: U14.A14 (IO_L10N_T1_16)
NCSI_TXD1: U14.C15 (IO_L3N_T0_DQS_16)
NCSI_TXEN: U14.B15 (IO_L7P_T1_16)
unnamed: R133.2, R161.1, U14.T19 (IO_L6P_T0_FCS_B_14)
PRSNT0_N_R: U14.C13 (IO_L8P_T1_16)
PUDC_B: R1.2, R2.1, U14.U22 (IO_L3P_T0_DQS_PUDC_B_14)
RGMII_CLK_FPGA: R207.2, U14.K19 (IO_L13N_T2_MRCC_15)
RGMII_REF_CLK: U14.H19 (IO_L12N_T1_MRCC_15)
RGMII_RXD0: R208.1
RGMII_RXD0_FPGA: R208.2, U14.L20 (IO_L14N_T2_SRCC_15)
RGMII_RXD1: R206.1
RGMII_RXD1_FPGA: R206.2, U14.L21 (IO_L10N_T1_AD11N_15)
RGMII_RXD2: R204.1
RGMII_RXD2_FPGA: R204.2, U14.K21 (IO_L9P_T1_DQS_AD3P_15)
RGMII_RXD3: R205.1
RGMII_RXD3_FPGA: R205.2, U14.K22 (IO_L9N_T1_DQS_AD3N_15)
RGMII_RX_CLK: R207.1
RGMII_RX_DV: R209.1
RGMII_RX_DV_FPGA: R209.2, U14.M22 (IO_L15N_T2_DQS_ADV_B_15)
RGMII_TXD0: U14.G20 (IO_L8N_T1_AD10N_15)
RGMII_TXD1: U14.H20 (IO_L8P_T1_AD10P_15)
RGMII_TXD2: U14.H22 (IO_L7N_T1_AD2N_15)
RGMII_TXD3: U14.J21 (IO_L11N_T1_SRCC_15)
RGMII_TX_CLK: U14.J19 (IO_L12P_T1_MRCC_15)
RGMII_TX_DV: U14.J22 (IO_L7P_T1_AD2P_15)
ROT_GPIO1: U14.N14 (IO_L23N_T3_A02_D18_14)
ROT_GPIO2: U14.U20 (IO_L11P_T1_SRCC_14)
ROT_MISO: U14.K13 (IO_L19P_T3_A22_15)
ROT_MOSI: U14.W20 (IO_L12N_T1_MRCC_14)
ROT_QSPI_CS_B: R161.2
ROT_QSPI_DQ0: U14.P22 (IO_L1P_T0_D00_MOSI_14)
ROT_QSPI_DQ1: U14.R22 (IO_L1N_T0_D01_DIN_14)
ROT_QSPI_DQ2: R134.2, U14.P21 (IO_L2P_T0_D02_14)
ROT_QSPI_DQ3: R135.2, U14.R21 (IO_L2N_T0_D03_14)
ROT_RDY\ROT_GPIO0: U14.F21 (IO_25_16)
ROT_RX: U14.G22 (IO_L24N_T3_16)
ROT_SCLK: U14.M16 (IO_L24N_T3_RS0_15)
ROT_SS: U14.M13 (IO_L20P_T3_A20_15)
ROT_TX: U14.F20 (IO_L18N_T2_16)
SGPIO_INTR_N: U14.M15 (IO_L24P_T3_RS1_15)
SPI0_CLK_R: U14.D20 (IO_L19P_T3_16)
SPI0_CS_N_R: U14.E22 (IO_L22P_T3_16)
SPI0_MISO_R: U14.D22 (IO_L22N_T3_16)
SPI0_MOSI_R: U14.E21 (IO_L23P_T3_16)
TPM_GPIO: U14.Y21 (IO_L9P_T1_DQS_14)
TPM_PIRQ#: U14.L16 (IO_L23P_T3_FOE_B_15)
TPM_PP: U14.M17 (IO_25_15)
TPM_RST: U14.R19 (IO_L5N_T0_D07_14)
UART0_SCM_RX: U14.D19 (IO_L14N_T2_SRCC_16)
UART0_SCM_TX: U14.A19 (IO_L17N_T2_16)
UART1_SCM_RX: U14.C19 (IO_L13N_T2_MRCC_16)
UART1_SCM_TX: U14.A16 (IO_L9N_T1_DQS_16)
ULPI1_CLKOUT: U14.W19 (IO_L12P_T1_MRCC_14)
ULPI1_DATA0: U14.AB18 (IO_L17N_T2_A13_D29_14)
ULPI1_DATA1: U14.AA18 (IO_L17P_T2_A14_D30_14)
ULPI1_DATA2: U14.AA19 (IO_L15P_T2_DQS_RDWR_B_14)
ULPI1_DATA3: U14.AB20 (IO_L15N_T2_DQS_DOUT_CSO_B_14)
ULPI1_DATA4: U14.AA20 (IO_L8P_T1_D11_14)
ULPI1_DATA5: U14.AB21 (IO_L10P_T1_D14_14)
ULPI1_DATA6: U14.AA21 (IO_L8N_T1_D12_14)
ULPI1_DATA7: U14.AB22 (IO_L10N_T1_D15_14)
ULPI1_DIR: U14.W21 (IO_L7P_T1_D09_14)
ULPI1_NXT: U14.W22 (IO_L7N_T1_D10_14)
ULPI1_RESET: U14.V20 (IO_L11N_T1_SRCC_14)
ULPI1_STP: U14.Y22 (IO_L9N_T1_DQS_D13_14)
USR_LED0: U14.T21 (IO_L4P_T0_D04_14)
USR_LED1: U14.U21 (IO_L4N_T0_D05_14)
USR_LED2: U14.V22 (IO_L3N_T0_DQS_EMCCLK_14)
VCC3V3: C92.2, C93.2, C94.2, C95.2, C98.2, C99.2, C100.2, C104.2, C105.2, C106.2, C110.2, C111.2, C112.2, C113.2, C116.2, C117.2, C118.2, C119.2, C122.2, C123.2, C124.2, C125.2, C128.2, C129.2, C130.2, C131.2, C233.2, C234.2, C235.2, C236.2, C238.2, C240.2, C259.2, C260.2, R1.1, R133.1, R134.1, R135.1, U14.[A17,B14,C21,D18,E1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 (VCCO_16), U14.[AA17,AB14,V16,W13,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 (VCCO_13), U14.[G19,H16,J13,K20,L1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 (VCCO_15), U14.[M14,P18,R15,T22,U1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 (VCCO_14), U15.1 (EN), U15.4 (VDD)
VIRTUAL_RESEAT_R: U14.B16 (IO_L7N_T1_16)

Notes on the sheet:
This bank is unavailable on 35T
