vollbert/artix-dc-scm/fpga-banks-34-25-cfg.kicad_sch

## KiCad design fpga-banks-34-25-cfg.kicad_sch (2026-04-19)

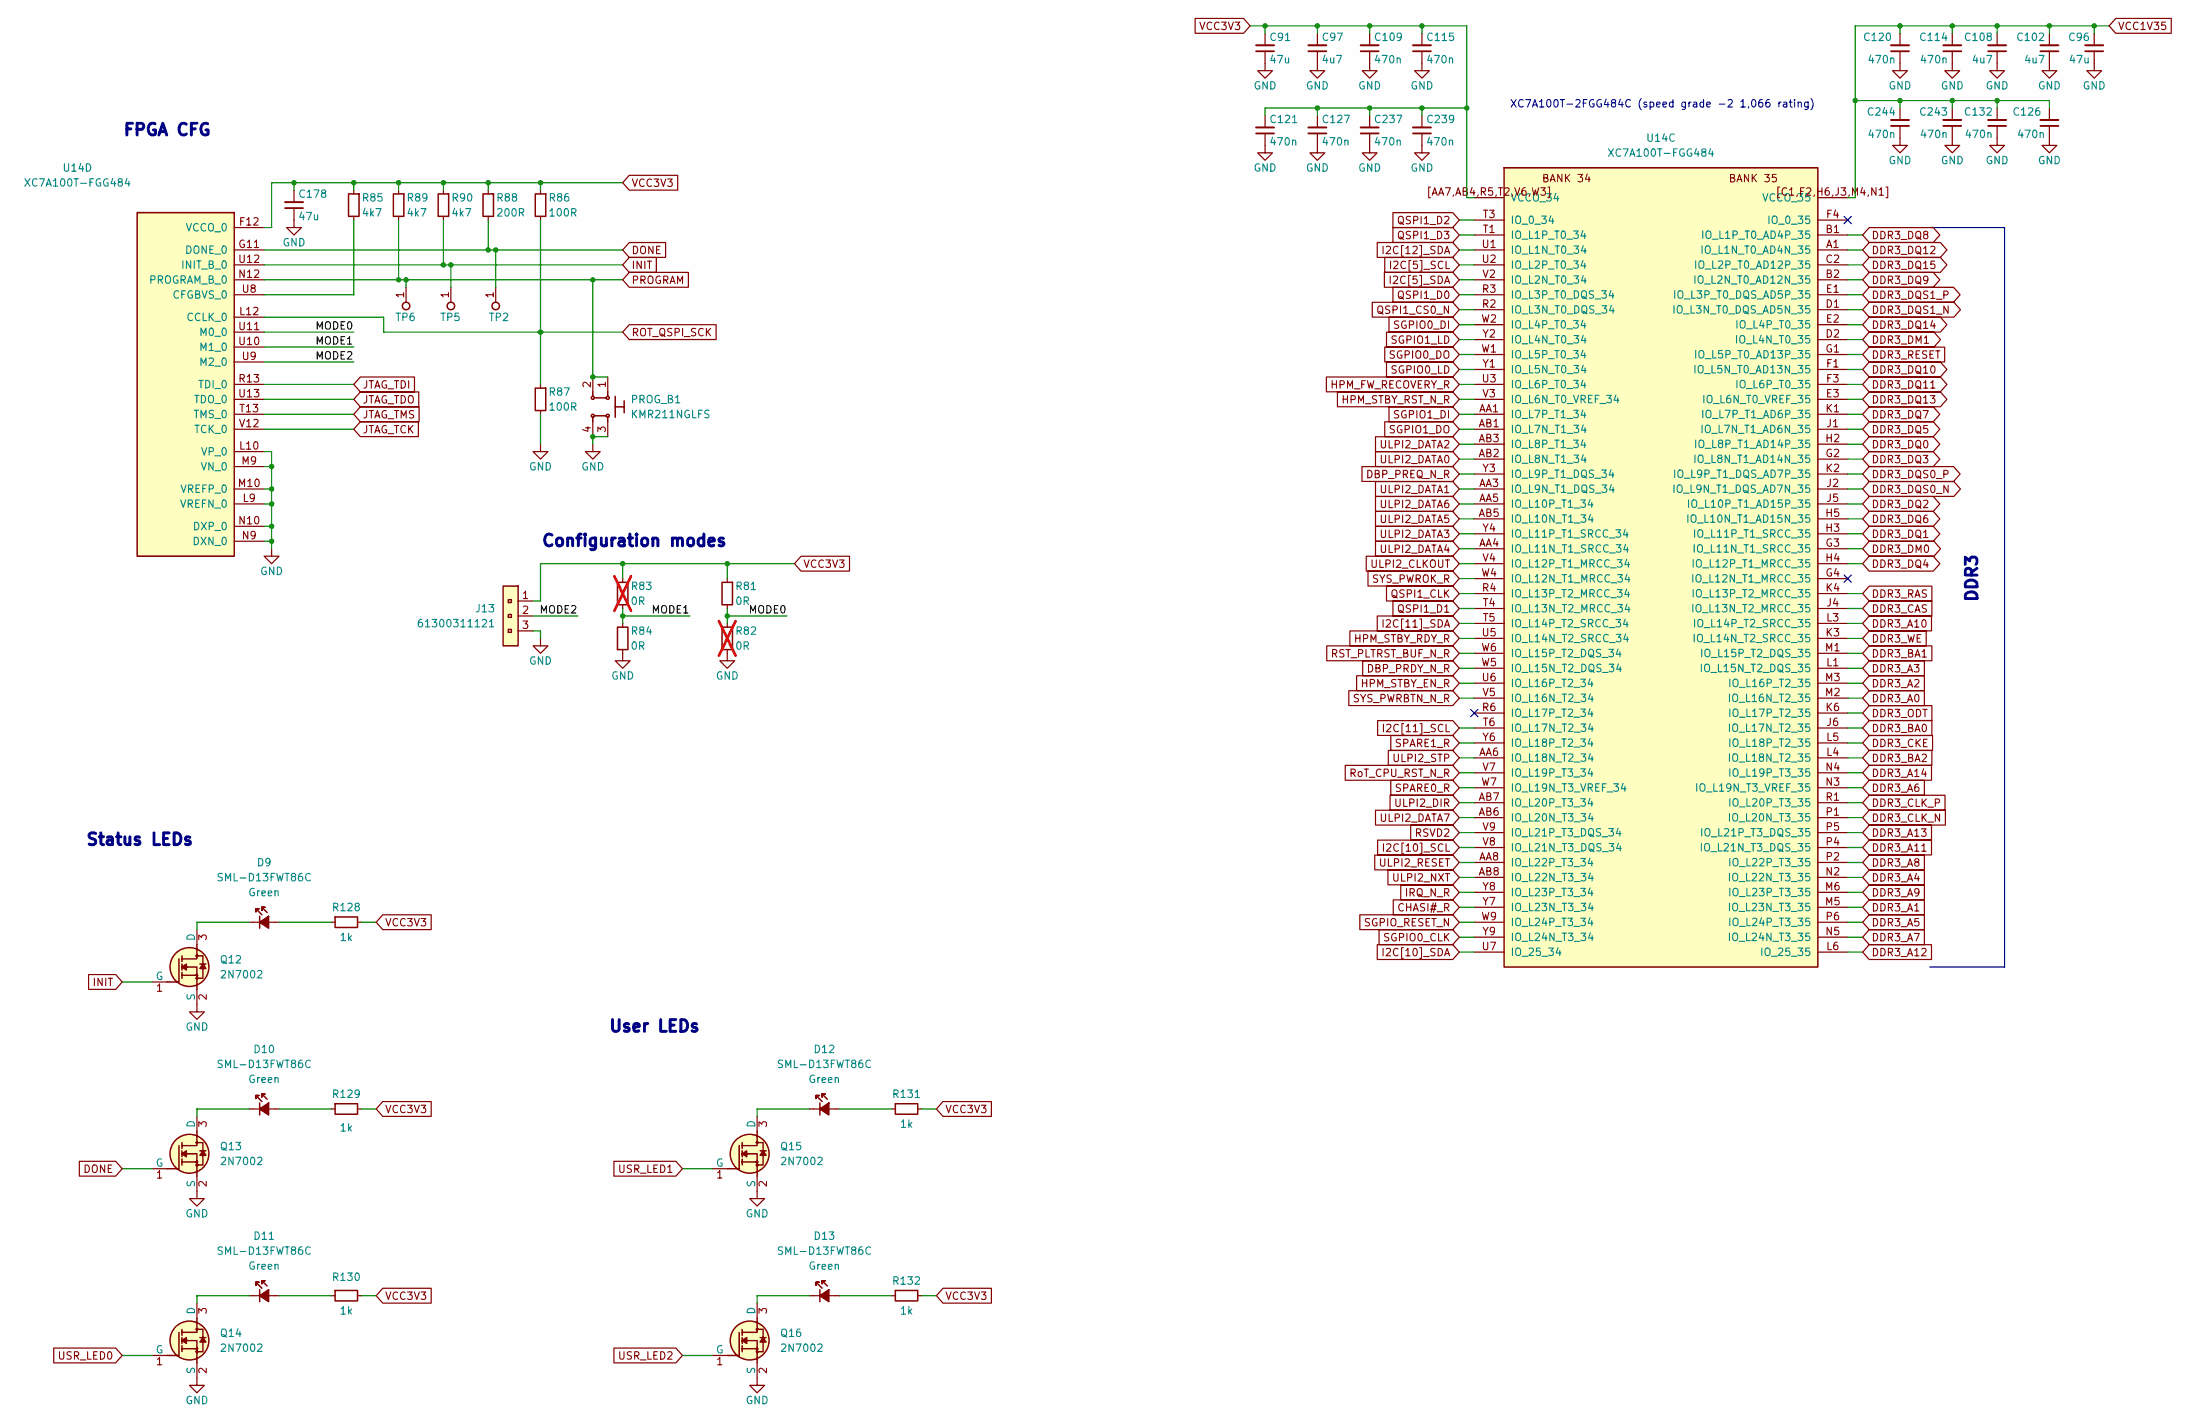
[picture p21: schematic fpga-banks-34-25-cfg.kicad_sch]

Parts:
C91, C96, C178: C_47u_1210; C_1210_3225Metric; MPN C1210C476K8RAC7210
C97, C102, C108: C_4u7_0603; C_0603_1608Metric; MPN C0603C475K9PAC
C109, C114, C115, C120, C121, C126, C127, C132, C237, C239, C243, C244: C_470n_0402; C_0402_1005Metric; MPN GXT155C80J474KE01D
D9, D10, D11, D12, D13: LED_G_0603_LG_L29K-G2J1-24-Z; LED_0603_1608Metric_G; MPN SML-D13FWT86C
J13: PinHeader_1x3_P2.54mm_Drill1.1mm; MPN 61300311121
PROG_B1: SW_KMR211NGLFS_SMD; MPN KMR211NGLFS
Q12, Q13, Q14, Q15, Q16: 2N7002_SOT-23-3; SOT-23-3; MPN 2N7002
R81, R84: R_0R_0402; R_0402_1005Metric; MPN RC0402JR-7D0RL
R82, R83: R_0R_0402; R_0402_1005Metric; MPN RC0402JR-7D0RL; not fitted
R85, R89, R90: R_4k7_0402; R_0402_1005Metric; Tolerance 1%; MPN RC0402FR-7D4K7L
R86, R87: R_100R_0402; R_0402_1005Metric; Tolerance 1%; MPN RC0402FR-7D100RL
R88: R_200R_0402; R_0402_1005Metric; Tolerance 1%; MPN CR0402-FX-2000GLF
R128, R129, R130, R131, R132: R_1k_0402; R_0402_1005Metric; Tolerance 1%; MPN CR0402-FX-1001GLF
TP2, TP5, TP6: TP_1mm_SMD; TP_SMD_1mm
U14: XC7A100T-FGG484; BGA-484_23x23mm_Layout22x22_P1mm_FGG484; MPN XC7A100T-2FGG484C

Connections:
CHASI#_R: U14.Y7 (IO_L23N_T3_34)
DBP_PRDY_N_R: U14.W5 (IO_L15N_T2_DQS_34)
DBP_PREQ_N_R: U14.Y3 (IO_L9P_T1_DQS_34)
DDR3_A0: U14.M2 (IO_L16N_T2_35)
DDR3_A1: U14.M5 (IO_L23N_T3_35)
DDR3_A2: U14.M3 (IO_L16P_T2_35)
DDR3_A3: U14.L1 (IO_L15N_T2_DQS_35)
DDR3_A4: U14.N2 (IO_L22N_T3_35)
DDR3_A5: U14.P6 (IO_L24P_T3_35)
DDR3_A6: U14.N3 (IO_L19N_T3_VREF_35)
DDR3_A7: U14.N5 (IO_L24N_T3_35)
DDR3_A8: U14.P2 (IO_L22P_T3_35)
DDR3_A9: U14.M6 (IO_L23P_T3_35)
DDR3_A10: U14.L3 (IO_L14P_T2_SRCC_35)
DDR3_A11: U14.P4 (IO_L21N_T3_DQS_35)
DDR3_A12: U14.L6 (IO_25_35)
DDR3_A13: U14.P5 (IO_L21P_T3_DQS_35)
DDR3_A14: U14.N4 (IO_L19P_T3_35)
DDR3_BA0: U14.J6 (IO_L17N_T2_35)
DDR3_BA1: U14.M1 (IO_L15P_T2_DQS_35)
DDR3_BA2: U14.L4 (IO_L18N_T2_35)
DDR3_CAS: U14.J4 (IO_L13N_T2_MRCC_35)
DDR3_CKE: U14.L5 (IO_L18P_T2_35)
DDR3_CLK_N: U14.P1 (IO_L20N_T3_35)
DDR3_CLK_P: U14.R1 (IO_L20P_T3_35)
DDR3_DM0: U14.G3 (IO_L11N_T1_SRCC_35)
DDR3_DM1: U14.D2 (IO_L4N_T0_35)
DDR3_DQ0: U14.H2 (IO_L8P_T1_AD14P_35)
DDR3_DQ1: U14.H3 (IO_L11P_T1_SRCC_35)
DDR3_DQ2: U14.J5 (IO_L10P_T1_AD15P_35)
DDR3_DQ3: U14.G2 (IO_L8N_T1_AD14N_35)
DDR3_DQ4: U14.H4 (IO_L12P_T1_MRCC_35)
DDR3_DQ5: U14.J1 (IO_L7N_T1_AD6N_35)
DDR3_DQ6: U14.H5 (IO_L10N_T1_AD15N_35)
DDR3_DQ7: U14.K1 (IO_L7P_T1_AD6P_35)
DDR3_DQ8: U14.B1 (IO_L1P_T0_AD4P_35)
DDR3_DQ9: U14.B2 (IO_L2N_T0_AD12N_35)
DDR3_DQ10: U14.F1 (IO_L5N_T0_AD13N_35)
DDR3_DQ11: U14.F3 (IO_L6P_T0_35)
DDR3_DQ12: U14.A1 (IO_L1N_T0_AD4N_35)
DDR3_DQ13: U14.E3 (IO_L6N_T0_VREF_35)
DDR3_DQ14: U14.E2 (IO_L4P_T0_35)
DDR3_DQ15: U14.C2 (IO_L2P_T0_AD12P_35)
DDR3_DQS0_N: U14.J2 (IO_L9N_T1_DQS_AD7N_35)
DDR3_DQS0_P: U14.K2 (IO_L9P_T1_DQS_AD7P_35)
DDR3_DQS1_N: U14.D1 (IO_L3N_T0_DQS_AD5N_35)
DDR3_DQS1_P: U14.E1 (IO_L3P_T0_DQS_AD5P_35)
DDR3_ODT: U14.K6 (IO_L17P_T2_35)
DDR3_RAS: U14.K4 (IO_L13P_T2_MRCC_35)
DDR3_RESET: U14.G1 (IO_L5P_T0_AD13P_35)
DDR3_WE: U14.K3 (IO_L14N_T2_SRCC_35)
DONE: Q13.1 (G), R88.2, TP2.1, U14.G11 (DONE_0)
GND: C91.1, C96.1, C97.1, C102.1, C108.1, C109.1, C114.1, C115.1, C120.1, C121.1, C126.1, C127.1, C132.1, C178.1, C237.1, C239.1, C243.1, C244.1, J13.3, PROG_B1.3, PROG_B1.4, Q12.2 (S), Q13.2 (S), Q14.2 (S), Q15.2 (S), Q16.2 (S), R82.1, R84.1, R87.2, U14.L9 (VREFN_0), U14.L10 (VP_0), U14.M9 (VN_0), U14.M10 (VREFP_0), U14.N9 (DXN_0), U14.N10 (DXP_0)
HPM_FW_RECOVERY_R: U14.U3 (IO_L6P_T0_34)
HPM_STBY_EN_R: U14.U6 (IO_L16P_T2_34)
HPM_STBY_RDY_R: U14.U5 (IO_L14N_T2_SRCC_34)
HPM_STBY_RST_N_R: U14.V3 (IO_L6N_T0_VREF_34)
I2C[5]_SCL: U14.U2 (IO_L2P_T0_34)
I2C[5]_SDA: U14.V2 (IO_L2N_T0_34)
I2C[10]_SCL: U14.V8 (IO_L21N_T3_DQS_34)
I2C[10]_SDA: U14.U7 (IO_25_34)
I2C[11]_SCL: U14.T6 (IO_L17N_T2_34)
I2C[11]_SDA: U14.T5 (IO_L14P_T2_SRCC_34)
I2C[12]_SDA: U14.U1 (IO_L1N_T0_34)
INIT: Q12.1 (G), R90.2, TP5.1, U14.U12 (INIT_B_0)
IRQ_N_R: U14.Y8 (IO_L23P_T3_34)
JTAG_TCK: U14.V12 (TCK_0)
JTAG_TDI: U14.R13 (TDI_0)
JTAG_TDO: U14.U13 (TDO_0)
JTAG_TMS: U14.T13 (TMS_0)
MODE0: R81.2, R82.2, U14.U11 (M0_0)
MODE1: R83.2, R84.2, U14.U10 (M1_0)
MODE2: J13.2, U14.U9 (M2_0)
unnamed: D9.1 (C), Q12.3 (D)
unnamed: D9.2 (A), R128.1
unnamed: D10.1 (C), Q13.3 (D)
unnamed: D10.2 (A), R129.1
unnamed: D11.1 (C), Q14.3 (D)
unnamed: D11.2 (A), R130.1
unnamed: D12.1 (C), Q15.3 (D)
unnamed: D12.2 (A), R131.1
unnamed: D13.1 (C), Q16.3 (D)
unnamed: D13.2 (A), R132.1
unnamed: R85.2, U14.U8 (CFGBVS_0)
PROGRAM: PROG_B1.1, PROG_B1.2, R89.2, TP6.1, U14.N12 (PROGRAM_B_0)
QSPI1_CLK: U14.R4 (IO_L13P_T2_MRCC_34)
QSPI1_CS0_N: U14.R2 (IO_L3N_T0_DQS_34)
QSPI1_D0: U14.R3 (IO_L3P_T0_DQS_34)
QSPI1_D1: U14.T4 (IO_L13N_T2_MRCC_34)
QSPI1_D2: U14.T3 (IO_0_34)
QSPI1_D3: U14.T1 (IO_L1P_T0_34)
ROT_QSPI_SCK: R86.2, R87.1, U14.L12 (CCLK_0)
RST_PLTRST_BUF_N_R: U14.W6 (IO_L15P_T2_DQS_34)
RSVD2: U14.V9 (IO_L21P_T3_DQS_34)
RoT_CPU_RST_N_R: U14.V7 (IO_L19P_T3_34)
SGPIO0_CLK: U14.Y9 (IO_L24N_T3_34)
SGPIO0_DI: U14.W2 (IO_L4P_T0_34)
SGPIO0_DO: U14.W1 (IO_L5P_T0_34)
SGPIO0_LD: U14.Y1 (IO_L5N_T0_34)
SGPIO1_DI: U14.AA1 (IO_L7P_T1_34)
SGPIO1_DO: U14.AB1 (IO_L7N_T1_34)
SGPIO1_LD: U14.Y2 (IO_L4N_T0_34)
SGPIO_RESET_N: U14.W9 (IO_L24P_T3_34)
SPARE0_R: U14.W7 (IO_L19N_T3_VREF_34)
SPARE1_R: U14.Y6 (IO_L18P_T2_34)
SYS_PWRBTN_N_R: U14.V5 (IO_L16N_T2_34)
SYS_PWROK_R: U14.W4 (IO_L12N_T1_MRCC_34)
ULPI2_CLKOUT: U14.V4 (IO_L12P_T1_MRCC_34)
ULPI2_DATA0: U14.AB2 (IO_L8N_T1_34)
ULPI2_DATA1: U14.AA3 (IO_L9N_T1_DQS_34)
ULPI2_DATA2: U14.AB3 (IO_L8P_T1_34)
ULPI2_DATA3: U14.Y4 (IO_L11P_T1_SRCC_34)
ULPI2_DATA4: U14.AA4 (IO_L11N_T1_SRCC_34)
ULPI2_DATA5: U14.AB5 (IO_L10N_T1_34)
ULPI2_DATA6: U14.AA5 (IO_L10P_T1_34)
ULPI2_DATA7: U14.AB6 (IO_L20N_T3_34)
ULPI2_DIR: U14.AB7 (IO_L20P_T3_34)
ULPI2_NXT: U14.AB8 (IO_L22N_T3_34)
ULPI2_RESET: U14.AA8 (IO_L22P_T3_34)
ULPI2_STP: U14.AA6 (IO_L18N_T2_34)
USR_LED0: Q14.1 (G)
USR_LED1: Q15.1 (G)
USR_LED2: Q16.1 (G)
VCC1V35: C96.2, C102.2, C108.2, C114.2, C120.2, C126.2, C132.2, C243.2, C244.2, U14.[C1,F2,H6,J3,M4,N1] (VCCO_35)
VCC3V3: C91.2, C97.2, C109.2, C115.2, C121.2, C127.2, C178.2, C237.2, C239.2, J13.1, R81.1, R83.1, R85.1, R86.1, R88.1, R89.1, R90.1, R128.2, R129.2, R130.2, R131.2, R132.2, U14.F12 (VCCO_0), U14.T12 (VCCO_0), U14.[AA7,AB4,R5,T2,V6,W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 (VCCO_34)

Notes on the sheet:
Status LEDs
DDR3
Configuration modes
FPGA CFG
XC7A100T-2FGG484C (speed grade -2 1,066 rating)
User LEDs
