vollbert/artix-dc-scm/fpga-power-supply.kicad_sch

## KiCad design fpga-power-supply.kicad_sch (2026-04-19)

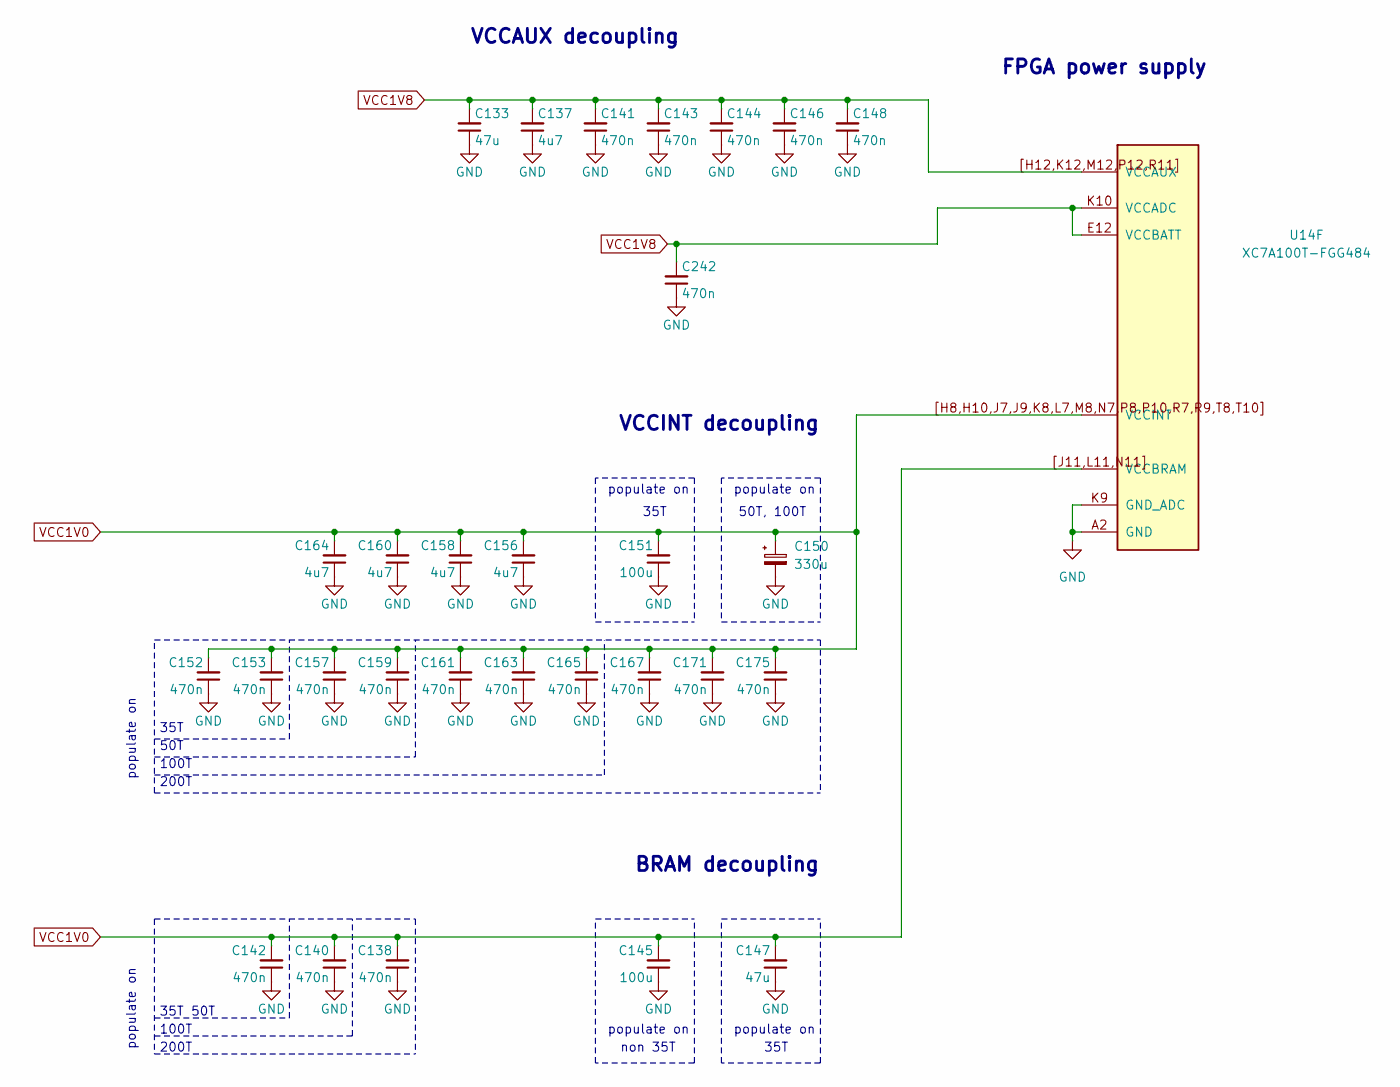
[picture p22: schematic fpga-power-supply.kicad_sch]

Parts:
C133, C147: C_47u_1210; C_1210_3225Metric; MPN C1210C476K8RAC7210
C137, C156, C158, C160, C164: C_4u7_0603; C_0603_1608Metric; MPN C0603C475K9PAC
C138, C140, C141, C142, C143, C144, C146, C148, C152, C153, C157, C159, C161, C163, C165, C167, C171, C175, C242: C_470n_0402; C_0402_1005Metric; MPN GXT155C80J474KE01D
C145, C151: C_100u_1210; C_1210_3225Metric; MPN CL32A107MQVNNNE
C150: C_Pol_330u_6.3V_KEMET-T520-D; C_Pol_EIA-D; Voltage 6.3V; MPN T520D337M006ATE045
U14: XC7A100T-FGG484; BGA-484_23x23mm_Layout22x22_P1mm_FGG484; MPN XC7A100T-2FGG484C

Connections:
GND: C133.1, C137.1, C138.1, C140.1, C141.1, C142.1, C143.1, C144.1, C145.1, C146.1, C147.1, C148.1, C150.2, C151.1, C152.1, C153.1, C156.1, C157.1, C158.1, C159.1, C160.1, C161.1, C163.1, C164.1, C165.1, C167.1, C171.1, C175.1, C242.1, U14.A2 (GND), U14.A3 (GND), U14.A5 (GND), U14.A7 (GND), U14.A9 (GND), U14.A11 (GND), U14.A12 (GND), U14.A22 (GND), U14.AA2 (GND), U14.AA12 (GND), U14.AA22 (GND), U14.AB9 (GND), U14.AB19 (GND), U14.B3 (GND), U14.B12 (GND), U14.B19 (GND), U14.C3 (GND), U14.C6 (GND), U14.C10 (GND), U14.C12 (GND), U14.C16 (GND), U14.D3 (GND), U14.D4 (GND), U14.D8 (GND), U14.D12 (GND), U14.D13 (GND), U14.E4 (GND), U14.E5 (GND), U14.E7 (GND), U14.E9 (GND), U14.E11 (GND), U14.E20 (GND), U14.F5 (GND), U14.F11 (GND), U14.F17 (GND), U14.G5 (GND), U14.G6 (GND), U14.G7 (GND), U14.G8 (GND), U14.G9 (GND), U14.G10 (GND), U14.G12 (GND), U14.G14 (GND), U14.H1 (GND), U14.H7 (GND), U14.H9 (GND), U14.H11 (GND), U14.H21 (GND), U14.J8 (GND), U14.J10 (GND), U14.J12 (GND), U14.J18 (GND), U14.K5 (GND), U14.K7 (GND), U14.K9 (GND_ADC), U14.K11 (GND), U14.K15 (GND), U14.L2 (GND), U14.L8 (GND), U14.L22 (GND), U14.M7 (GND), U14.M11 (GND), U14.M19 (GND), U14.N6 (GND), U14.N8 (GND), U14.N16 (GND), U14.P3 (GND), U14.P7 (GND), U14.P9 (GND), U14.P11 (GND), U14.P13 (GND), U14.R8 (GND), U14.R10 (GND), U14.R12 (GND), U14.R20 (GND), U14.T7 (GND), U14.T9 (GND), U14.T11 (GND), U14.T17 (GND), U14.U4 (GND), U14.U14 (GND), U14.V1 (GND), U14.V11 (GND), U14.V21 (GND), U14.W8 (GND), U14.W18 (GND), U14.Y5 (GND), U14.Y15 (GND)
VCC1V0: C138.2, C140.2, C142.2, C145.2, C147.2, C150.1, C151.2, C152.2, C153.2, C156.2, C157.2, C158.2, C159.2, C160.2, C161.2, C163.2, C164.2, C165.2, C167.2, C171.2, C175.2, U14.[H8,H10,J7,J9,K8,L7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 (VCCINT), U14.[J11,L11,N11] (VCCBRAM)
VCC1V8: C133.2, C137.2, C141.2, C143.2, C144.2, C146.2, C148.2, C242.2, U14.E12 (VCCBATT), U14.K10 (VCCADC), U14.[H12,K12,M12,P12,R1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 (VCCAUX)

Notes on the sheet:
populate on
35T
200T
50T
35T
100T
VCCINT decoupling
VCCAUX decoupling
50T, 100T
BRAM decoupling
FPGA power supply
non 35T
