vollbert/artix-dc-scm/interfaces.kicad_sch

## KiCad design interfaces.kicad_sch (2026-04-19)

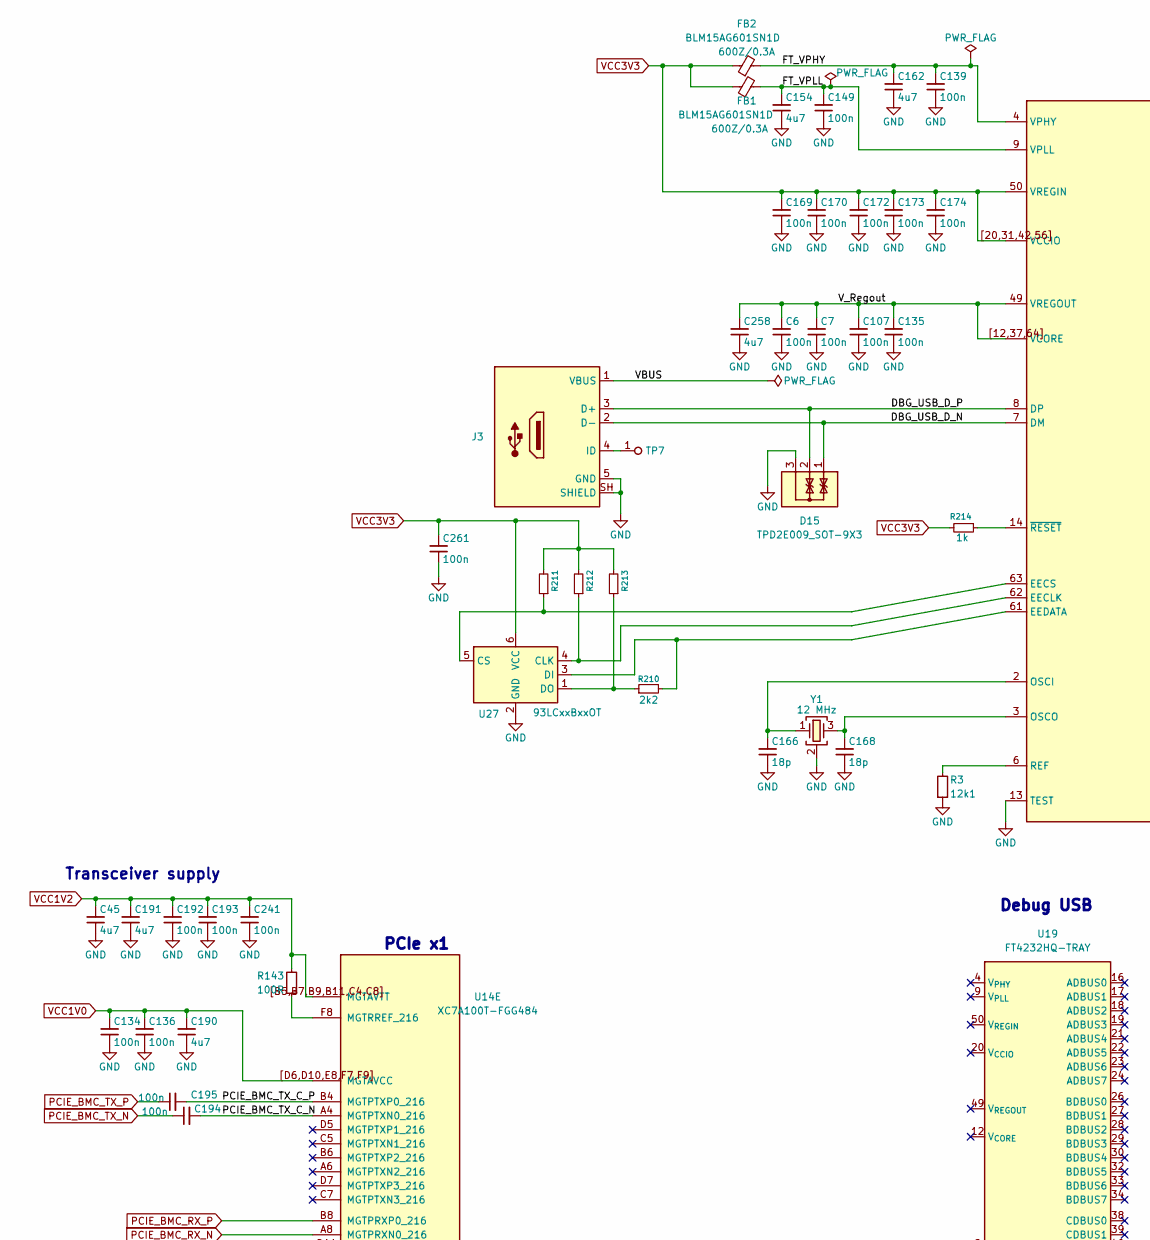
[picture p23: schematic interfaces.kicad_sch, part in row 1, column 1]

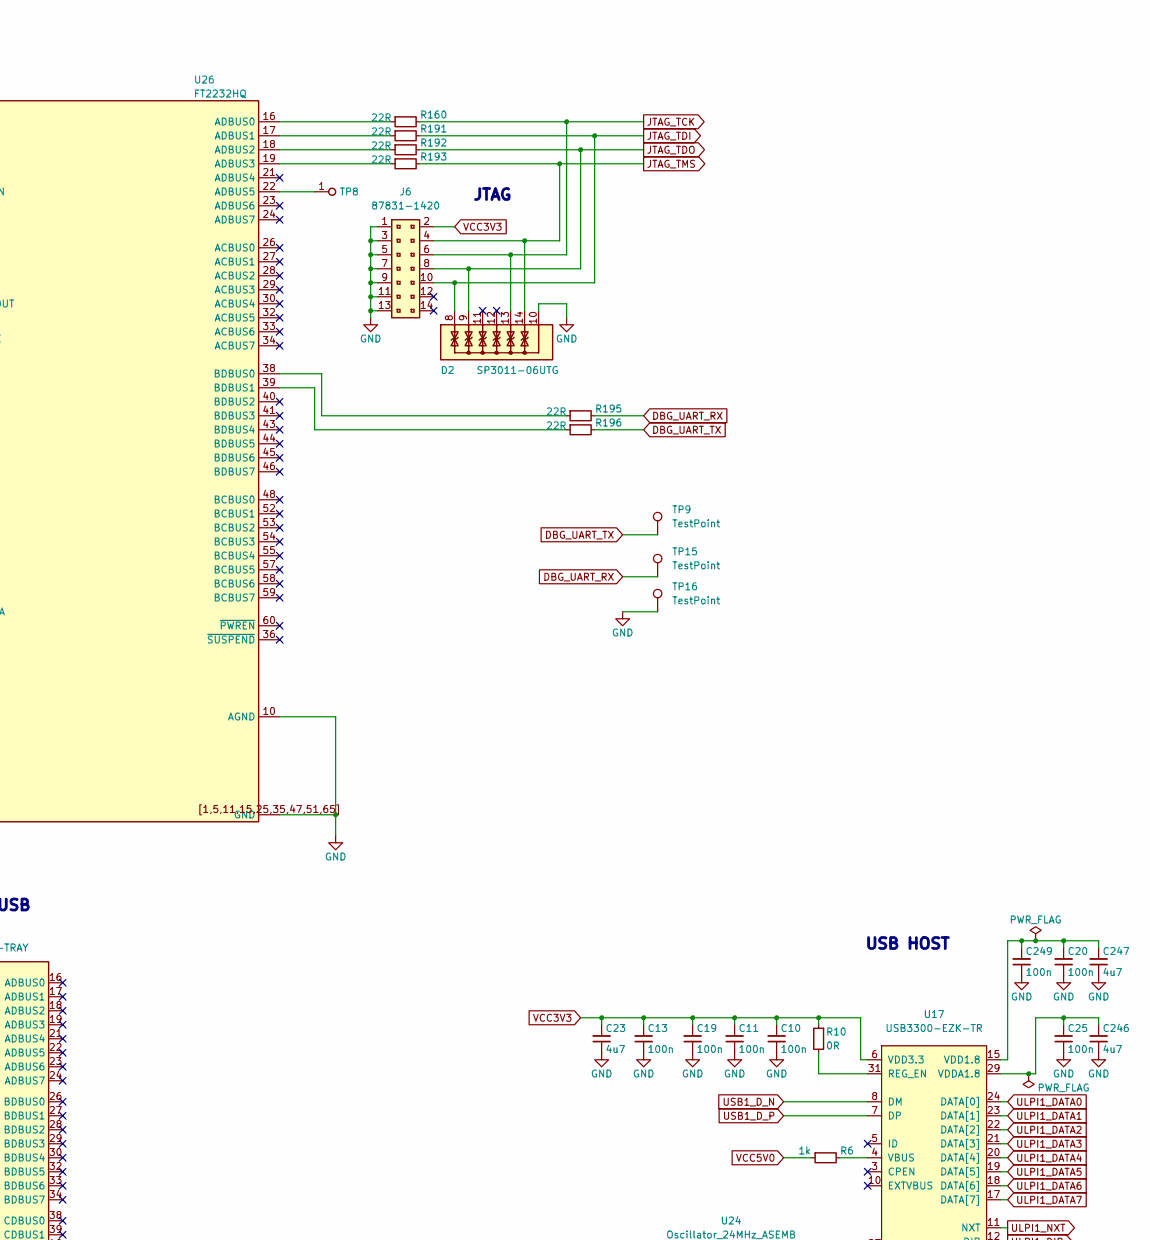
[picture p24: schematic interfaces.kicad_sch, part in row 1, column 2]

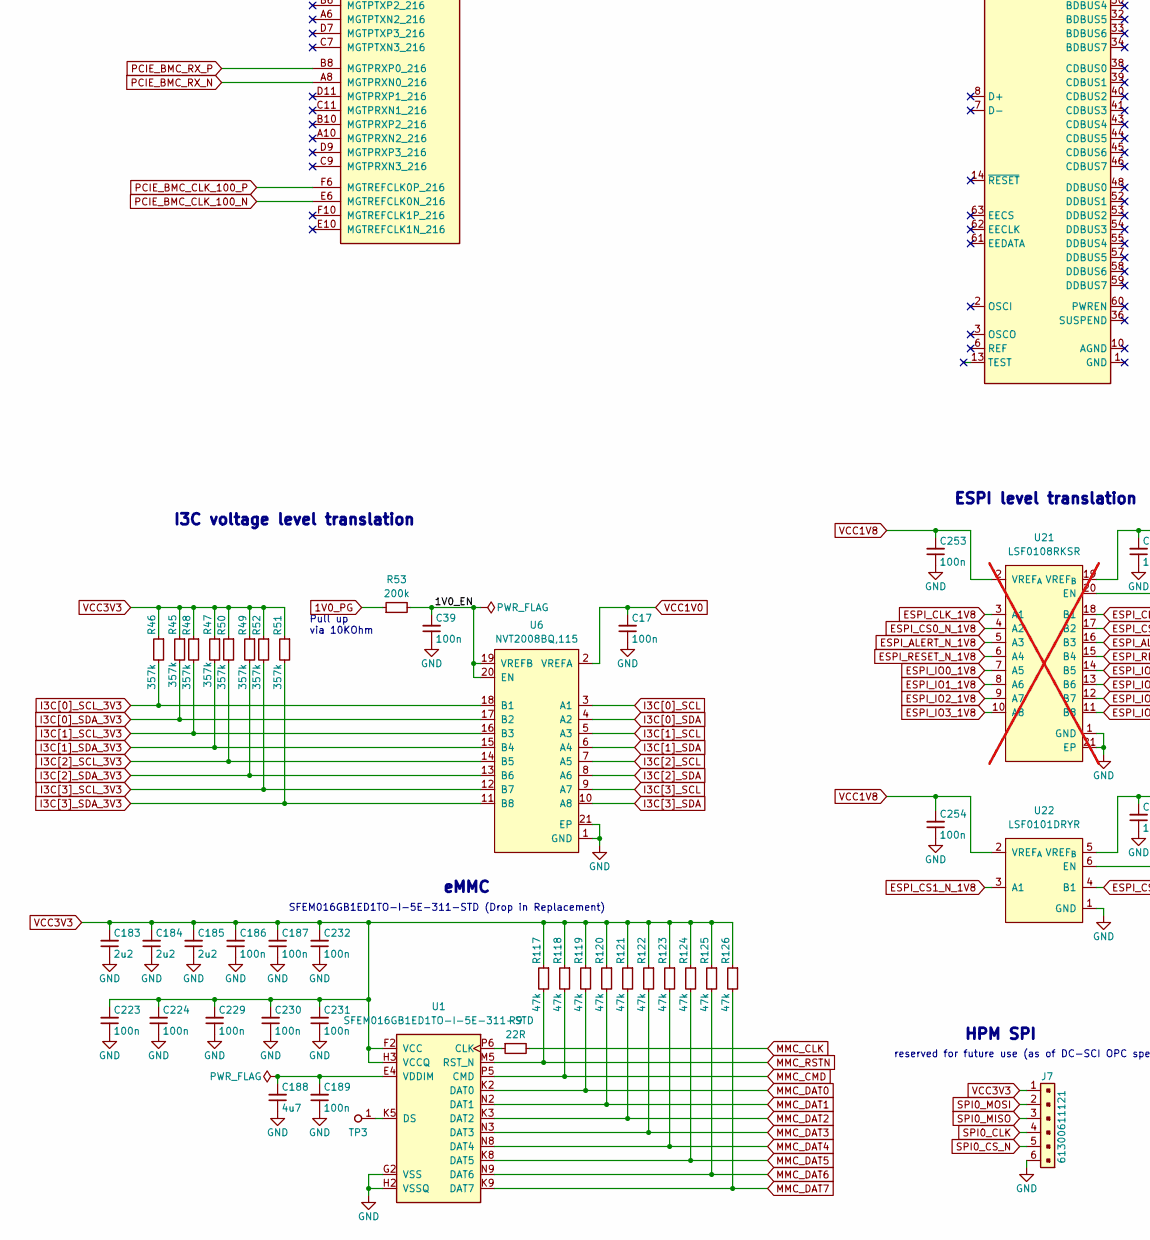
[picture p25: schematic interfaces.kicad_sch, part in row 2, column 1]

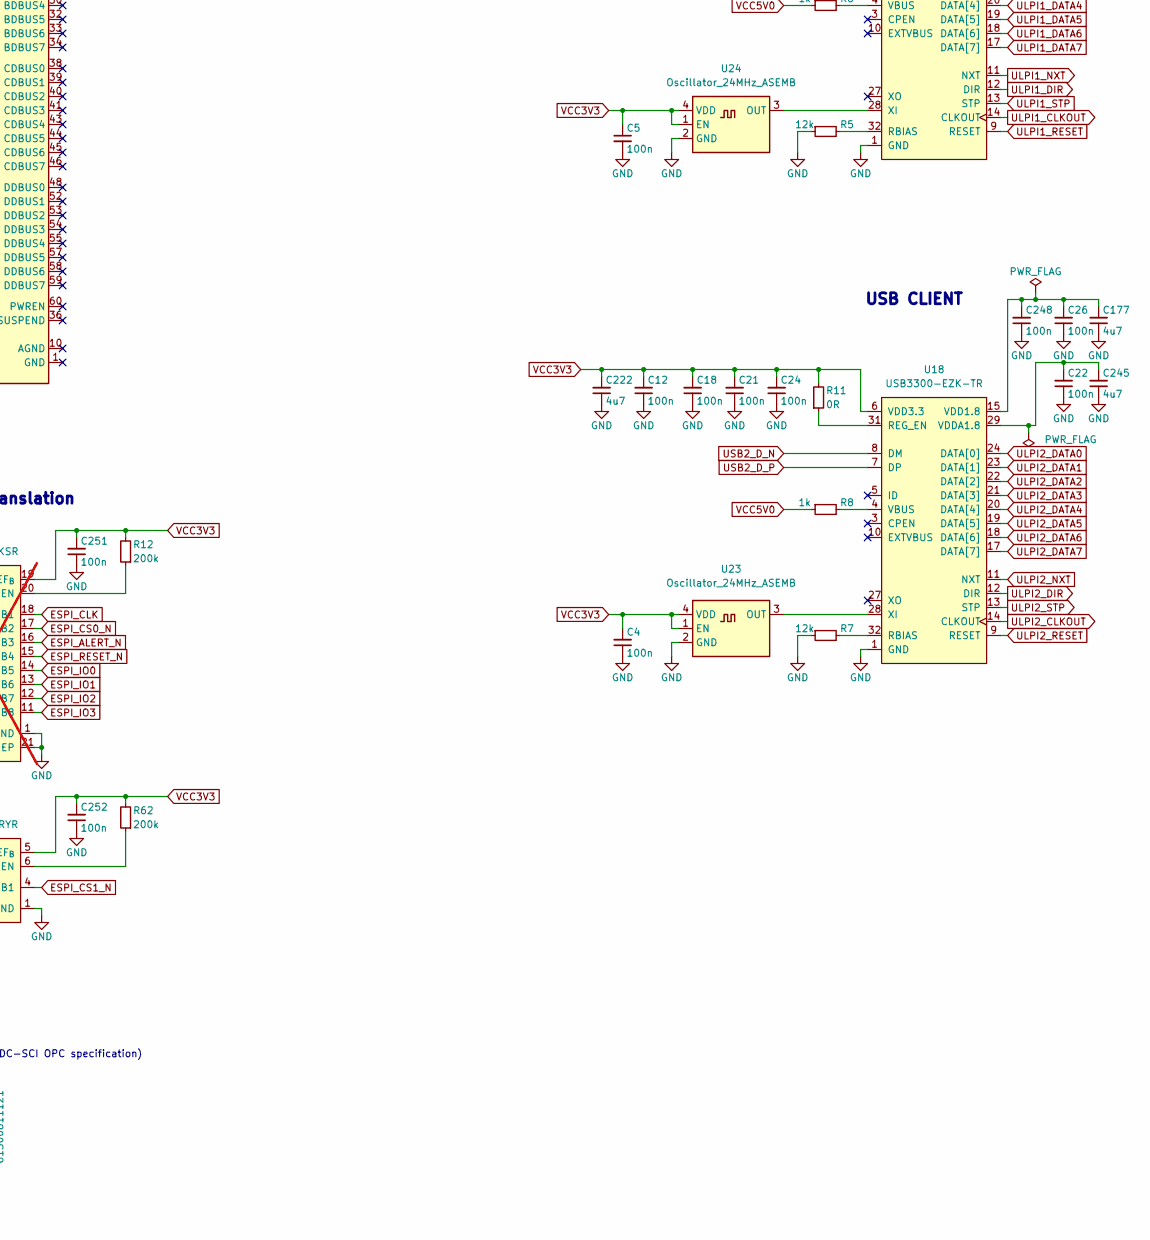
[picture p26: schematic interfaces.kicad_sch, part in row 2, column 2]

Parts:
C4, C5, C6, C7, C10, C11, C12, C13, C18, C19, C20, C21, C22, C24, C25, C26, C107, C135, C139, C149, C169, C170, C172, C173, C174, C248, C249, C251, C252, C253, C254, C261: C_100n_0402; C_0402_1005Metric; Voltage 50V; MPN GRM155R61H104KE14D
C17, C39, C134, C136, C186, C187, C189, C192, C193, C194, C195, C223, C224, C229, C230, C231, C232, C241: C_100n_6V3_0402; C_0402_1005Metric; MPN 0402X104K6R3CT
C23, C154, C162, C177, C188, C222, C245, C246, C247, C258: C_4u7_0402; C_0402_1005Metric; MPN GRM155R61A475MEAAD
C45, C190, C191: C_4u7_0603; C_0603_1608Metric; MPN C0603C475K9PAC
C166, C168: C_18p_0402; C_0402_1005Metric; MPN CL05C180JB51PNC
C183, C184, C185: C_2u2_0402; C_0402_1005Metric; MPN C1005X5R1A225K050BC
D2: SP3011-06UTG; USON-14_3.5x1.35_P0.5mm; MPN SP3011-06UTG
D15: TPD2E009_SOT-9X3; SOT-723; MPN TPD2E009DRTR
FB1, FB2: FB_600Z_0.3A_Murata-BLM15AG_0402; FB_0402_1005Metric; MPN BLM15AG601SN1D
J3: USB-Micro-B_Amphenol_10118192-0001LF; USB-Micro-B_Receptacle_Amphenol_10118192; MPN 10118192-0001LF
J6: PinHeader_2x7_P2mm_Drill0.9mm_878311420; MPN 87831-1420
J7: PinHeader_1x6_P2.54mm_Drill1.1mm; MPN 61300611121
R3: R_12k1_0402; R_0402_1005Metric; Tolerance 1%; MPN CR0402-FX-1212GLF
R5, R7: R_12k_0402; R_0402_1005Metric; Tolerance 1%; MPN CR0402-FX-1202GLF
R6, R8: R_1k_0402; R_0402_1005Metric; Tolerance 1%; MPN CR0402-FX-1001GLF
R9, R160, R191, R192, R193, R195, R196: R_22R_0402; R_0402_1005Metric; Tolerance 1%; MPN RC0402FR-7D22RL
R10, R11: R_0R_0402; R_0402_1005Metric; MPN RC0402JR-7D0RL
R12, R53, R62: R_200k_0402; R_0402_1005Metric; Tolerance 1%; MPN CR0402-FX-2003GLF
R45, R46, R47, R48, R49, R50, R51, R52: R_357k_0402; R_0402_1005Metric; Tolerance 1%; MPN CR0402-FX-3573GLF
R117, R118, R119, R120, R121, R122, R123, R124, R125, R126: R_47k_0402; R_0402_1005Metric; Tolerance 1%; MPN CR0402-FX-4702GLF
R143: R_100R_0402; R_0402_1005Metric; Tolerance 1%; MPN RC0402FR-7D100RL
R210: R_2k2_0402; R_0402_1005Metric; MPN AC0402FR-7D2K2L
R211, R212, R213: R_10k_0402; R_0402_1005Metric; MPN CR0402AFX-1002GAS
R214: R_1k_0402; R_0402_1005Metric; MPN CR0402-FX-1001GLF
TP3, TP7, TP8: TP_1mm_SMD; TP_SMD_1mm
TP9, TP15, TP16: TestPoint; TestPoint_Pad_D1.0mm
U1: SFEM016GB1ED1TO-I-5E-311-STD; BGA-170-100_18x14mm_Layout17x10_P1mm; MPN SFEM016GB1ED1TO-I-5E-311-STD
U6: NVT2008BQ,115; VQFN-20_1EP_4.5x2.5mm_P0.5mm; MPN NVT2008BQ,115
U14: XC7A100T-FGG484; BGA-484_23x23mm_Layout22x22_P1mm_FGG484; MPN XC7A100T-2FGG484C
U17, U18: USB3300-EZK-TR; QFN-32-1EP_5x5mm; MPN USB3300-EZK-TR
U19: FT4232H_QFN; QFN-64-1EP_9x9mm_P0.5mm; MPN FT4232HQ-TRAY
U21: LSF0108RKSR; VQFN-20_1EP_4.5x2.5mm_P0.5mm; MPN LSF0108RKSR; not fitted
U22: LSF0101DRYR; USON-6_1.45x1.0mm_P0.5mm_Texas_DRY6; MPN LSF0101DRYR
U23, U24: Oscillator_24MHz_ASEMB; Oscillator_SMD_Abracon_ASEMB_3.2x2.5mm; MPN ASEMB-24.000MHZ-LC-T
U26: FT2232HQ; QFN-64-1EP_9x9mm_P0.5mm_EP4.35x4.35mm; MPN FT2232HQ-REEL
U27: 93LCxxBxxOT; SOT-23-6; MPN 93LC66BT-I/OT
Y1: Resonator_12MHz_ABM8G; Resonator_SMD_Abracon_ABM8G_3.2x2.5mm; MPN ABM8G-12.000MHZ-18-D2Y-T

Connections:
1V0_EN: C39.2, R53.2, U6.19 (VREFB), U6.20 (EN)
1V0_PG: R53.1
DBG_UART_RX: R195.2, TP15.1
DBG_UART_TX: R196.2, TP9.1
DBG_USB_D_N: D15.1, J3.2 (D-), U26.7 (DM)
DBG_USB_D_P: D15.2, J3.3 (D+), U26.8 (DP)
ESPI_ALERT_N: U21.16 (B3)
ESPI_ALERT_N_1V8: U21.5 (A3)
ESPI_CLK: U21.18 (B1)
ESPI_CLK_1V8: U21.3 (A1)
ESPI_CS0_N: U21.17 (B2)
ESPI_CS0_N_1V8: U21.4 (A2)
ESPI_CS1_N: U22.4 (B1)
ESPI_CS1_N_1V8: U22.3 (A1)
ESPI_IO0: U21.14 (B5)
ESPI_IO0_1V8: U21.7 (A5)
ESPI_IO1: U21.13 (B6)
ESPI_IO1_1V8: U21.8 (A6)
ESPI_IO2: U21.12 (B7)
ESPI_IO2_1V8: U21.9 (A7)
ESPI_IO3: U21.11 (B8)
ESPI_IO3_1V8: U21.10 (A8)
ESPI_RESET_N: U21.15 (B4)
ESPI_RESET_N_1V8: U21.6 (A4)
FT_VPHY: C139.2, C162.2, FB2.2, U26.4 (VPHY)
FT_VPLL: C149.2, C154.2, FB1.2, U26.9 (VPLL)
GND: C4.1, C5.2, C6.1, C7.1, C10.1, C11.1, C12.1, C13.1, C17.1, C18.1, C19.1, C20.1, C21.1, C22.1, C23.1, C24.1, C25.1, C26.1, C39.1, C45.1, C107.1, C134.1, C135.1, C136.1, C139.1, C149.1, C154.1, C162.1, C166.1, C168.1, C169.1, C170.1, C172.1, C173.1, C174.1, C177.1, C183.1, C184.1, C185.1, C186.1, C187.1, C188.1, C189.1, C190.1, C191.1, C192.1, C193.1, C222.1, C223.1, C224.1, C229.1, C230.1, C231.1, C232.1, C241.1, C245.1, C246.1, C247.1, C248.1, C249.1, C251.1, C252.1, C253.1, C254.1, C258.1, C261.1, D2.5, D2.10, D15.3, J3.5 (GND), J3.SH (SHIELD), J6.1, J6.3, J6.5, J6.7, J6.9, J6.11, J6.13, J7.6, R3.1, R5.1, R7.1, TP16.1, U1.G2 (VSS), U1.G3 (VSS), U1.G4 (VSS), U1.G5 (VSS), U1.G6 (VSS), U1.G7 (VSS), U1.G8 (VSS), U1.G9 (VSS), U1.H2 (VSSQ), U1.H9 (VSSQ), U1.J5 (VSS), U1.L3 (VSSQ), U1.L8 (VSSQ), U1.M4 (VSSQ), U1.M7 (VSSQ), U1.P2 (VSSQ), U1.P9 (VSSQ), U6.1 (GND), U6.21 (EP), U17.1 (GND), U17.2 (GND), U17.33 (EP), U18.1 (GND), U18.2 (GND), U18.33 (EP), U21.1 (GND), U21.21 (EP), U22.1 (GND), U23.2 (GND), U24.2 (GND), U26.10 (AGND), U26.13 (TEST), U26.[1,5,11,15,25,35,47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 (GND), U27.2 (GND), Y1.2 (SH), Y1.4 (SH)
I3C[0]_SCL: U6.3 (A1)
I3C[0]_SCL_3V3: R46.2, U6.18 (B1)
I3C[0]_SDA: U6.4 (A2)
I3C[0]_SDA_3V3: R45.2, U6.17 (B2)
I3C[1]_SCL: U6.5 (A3)
I3C[1]_SCL_3V3: R48.2, U6.16 (B3)
I3C[1]_SDA: U6.6 (A4)
I3C[1]_SDA_3V3: R47.2, U6.15 (B4)
I3C[2]_SCL: U6.7 (A5)
I3C[2]_SCL_3V3: R50.2, U6.14 (B5)
I3C[2]_SDA: U6.8 (A6)
I3C[2]_SDA_3V3: R49.2, U6.13 (B6)
I3C[3]_SCL: U6.9 (A7)
I3C[3]_SCL_3V3: R52.2, U6.12 (B7)
I3C[3]_SDA: U6.10 (A8)
I3C[3]_SDA_3V3: R51.2, U6.11 (B8)
JTAG_TCK: D2.2, D2.13, J6.6, R160.2
JTAG_TDI: D2.7, D2.8, J6.10, R191.2
JTAG_TDO: D2.6, D2.9, J6.8, R192.2
JTAG_TMS: D2.1, D2.14, J6.4, R193.2
MMC_CLK: R9.2
MMC_CMD: R118.2, U1.P5 (CMD)
MMC_DAT0: R119.2, U1.K2 (DAT0)
MMC_DAT1: R120.2, U1.N2 (DAT1)
MMC_DAT2: R121.2, U1.K3 (DAT2)
MMC_DAT3: R122.2, U1.N3 (DAT3)
MMC_DAT4: R123.2, U1.N8 (DAT4)
MMC_DAT5: R124.2, U1.K8 (DAT5)
MMC_DAT6: R125.2, U1.N9 (DAT6)
MMC_DAT7: R126.2, U1.K9 (DAT7)
MMC_RSTN: R117.2, U1.M5 (RST_N)
unnamed: C20.2, C247.2, C249.2, U17.15 (VDD1.8), U17.26 (VDD1.8)
unnamed: C22.2, C245.2, U18.29 (VDDA1.8)
unnamed: C166.2, U26.2 (OSCI), Y1.1
unnamed: C168.2, U26.3 (OSCO), Y1.3
unnamed: C26.2, C177.2, C248.2, U18.15 (VDD1.8), U18.26 (VDD1.8)
unnamed: C188.2, C189.2, U1.E4 (VDDIM)
unnamed: C25.2, C246.2, U17.29 (VDDA1.8)
unnamed: D2.4, D2.11
unnamed: D2.3, D2.12
unnamed: J3.4 (ID), TP7.1
unnamed: R3.2, U26.6 (REF)
unnamed: R5.2, U17.32 (RBIAS)
unnamed: R6.2, U17.4 (VBUS)
unnamed: R7.2, U18.32 (RBIAS)
unnamed: R8.2, U18.4 (VBUS)
unnamed: R9.1, U1.P6 (CLK)
unnamed: R10.2, U17.31 (REG_EN)
unnamed: R11.1, U18.31 (REG_EN)
unnamed: R12.1, U21.20 (EN)
unnamed: R62.1, U22.6 (EN)
unnamed: R143.1, U14.F8 (MGTRREF_216)
unnamed: R160.1, U26.16 (ADBUS0)
unnamed: R191.1, U26.17 (ADBUS1)
unnamed: R192.1, U26.18 (ADBUS2)
unnamed: R193.1, U26.19 (ADBUS3)
unnamed: R195.1, U26.38 (BDBUS0)
unnamed: R196.1, U26.39 (BDBUS1)
unnamed: R210.1, R213.1, U27.1 (DO)
unnamed: R210.2, U26.61 (EEDATA), U27.3 (DI)
unnamed: R211.1, U26.63 (EECS), U27.5 (CS)
unnamed: R212.1, U26.62 (EECLK), U27.4 (CLK)
unnamed: R214.1, U26.14 (~RESET)
unnamed: TP3.1, U1.K5 (DS)
unnamed: TP8.1, U26.22 (ADBUS5)
unnamed: U17.28 (XI), U24.3 (OUT)
unnamed: U18.28 (XI), U23.3 (OUT)
unnamed: U19.1 (GND), U19.5 (GND), U19.11 (GND), U19.15 (GND), U19.25 (GND), U19.35 (GND), U19.47 (GND), U19.51 (GND), U19.65 (GND)
unnamed: U19.12 (V_{CORE}), U19.37 (V_{CORE}), U19.64 (V_{CORE})
unnamed: U19.20 (V_{CCIO}), U19.31 (V_{CCIO}), U19.42 (V_{CCIO}), U19.56 (V_{CCIO})
PCIE_BMC_CLK_100_N: U14.E6 (MGTREFCLK0N_216)
PCIE_BMC_CLK_100_P: U14.F6 (MGTREFCLK0P_216)
PCIE_BMC_RX_N: U14.A8 (MGTPRXN0_216)
PCIE_BMC_RX_P: U14.B8 (MGTPRXP0_216)
PCIE_BMC_TX_C_N: C194.2, U14.A4 (MGTPTXN0_216)
PCIE_BMC_TX_C_P: C195.2, U14.B4 (MGTPTXP0_216)
PCIE_BMC_TX_N: C194.1
PCIE_BMC_TX_P: C195.1
SPI0_CLK: J7.4
SPI0_CS_N: J7.5
SPI0_MISO: J7.3
SPI0_MOSI: J7.2
ULPI1_CLKOUT: U17.14 (CLKOUT)
ULPI1_DATA0: U17.24 (DATA[0])
ULPI1_DATA1: U17.23 (DATA[1])
ULPI1_DATA2: U17.22 (DATA[2])
ULPI1_DATA3: U17.21 (DATA[3])
ULPI1_DATA4: U17.20 (DATA[4])
ULPI1_DATA5: U17.19 (DATA[5])
ULPI1_DATA6: U17.18 (DATA[6])
ULPI1_DATA7: U17.17 (DATA[7])
ULPI1_DIR: U17.12 (DIR)
ULPI1_NXT: U17.11 (NXT)
ULPI1_RESET: U17.9 (RESET)
ULPI1_STP: U17.13 (STP)
ULPI2_CLKOUT: U18.14 (CLKOUT)
ULPI2_DATA0: U18.24 (DATA[0])
ULPI2_DATA1: U18.23 (DATA[1])
ULPI2_DATA2: U18.22 (DATA[2])
ULPI2_DATA3: U18.21 (DATA[3])
ULPI2_DATA4: U18.20 (DATA[4])
ULPI2_DATA5: U18.19 (DATA[5])
ULPI2_DATA6: U18.18 (DATA[6])
ULPI2_DATA7: U18.17 (DATA[7])
ULPI2_DIR: U18.12 (DIR)
ULPI2_NXT: U18.11 (NXT)
ULPI2_RESET: U18.9 (RESET)
ULPI2_STP: U18.13 (STP)
USB1_D_N: U17.8 (DM)
USB1_D_P: U17.7 (DP)
USB2_D_N: U18.8 (DM)
USB2_D_P: U18.7 (DP)
VBUS: J3.1 (VBUS)
VCC1V0: C17.2, C134.2, C136.2, C190.2, U6.2 (VREFA), U14.[D6,D10,E8,F7,F9] (MGTAVCC)
VCC1V2: C45.2, C191.2, C192.2, C193.2, C241.2, R143.2, U14.[B5,B7,B9,B11,C4,C8] (MGTAVTT)
VCC1V8: C253.2, C254.2, U21.2 (VREF_{A}), U22.2 (VREF_{A})
VCC3V3: C4.2, C5.1, C10.2, C11.2, C12.2, C13.2, C18.2, C19.2, C21.2, C23.2, C24.2, C169.2, C170.2, C172.2, C173.2, C174.2, C183.2, C184.2, C185.2, C186.2, C187.2, C222.2, C223.2, C224.2, C229.2, C230.2, C231.2, C232.2, C251.2, C252.2, C261.2, FB1.1, FB2.1, J6.2, J7.1, R10.1, R11.2, R12.2, R45.1, R46.1, R47.1, R48.1, R49.1, R50.1, R51.1, R52.1, R62.2, R117.1, R118.1, R119.1, R120.1, R121.1, R122.1, R123.1, R124.1, R125.1, R126.1, R211.2, R212.2, R213.2, R214.2, U1.F2 (VCC), U1.F3 (VCC), U1.F4 (VCC), U1.F5 (VCC), U1.F6 (VCC), U1.F7 (VCC), U1.F8 (VCC), U1.F9 (VCC), U1.H3 (VCCQ), U1.H8 (VCCQ), U1.L2 (VCCQ), U1.L4 (VCCQ), U1.L7 (VCCQ), U1.L9 (VCCQ), U1.P3 (VCCQ), U1.P8 (VCCQ), U17.6 (VDD3.3), U17.16 (VDD3.3), U17.25 (VDD3.3), U17.30 (VDD3.3), U18.6 (VDD3.3), U18.16 (VDD3.3), U18.25 (VDD3.3), U18.30 (VDD3.3), U21.19 (VREF_{B}), U22.5 (VREF_{B}), U23.1 (EN), U23.4 (VDD), U24.1 (EN), U24.4 (VDD), U26.50 (VREGIN), U26.[20,31,42,56] (VCCIO), U27.6 (VCC)
VCC5V0: R6.1, R8.1
V_Regout: C6.2, C7.2, C107.2, C135.2, C258.2, U26.49 (VREGOUT), U26.[12,37,64] (VCORE)

Notes on the sheet:
SFEM016GB1ED1TO-I-5E-311-STD (Drop in Replacement)
USB CLIENT
eMMC
Transceiver supply
Pull up via 10KOhm
PCIe x1
Debug USB
JTAG
HPM SPI
reserved for future use (as of DC-SCI OPC specification)
USB HOST
ESPI level translation
I3C voltage level translation
