vollbert/artix-dc-scm/pcie-conn.kicad_sch

## KiCad design pcie-conn.kicad_sch (2026-04-19)

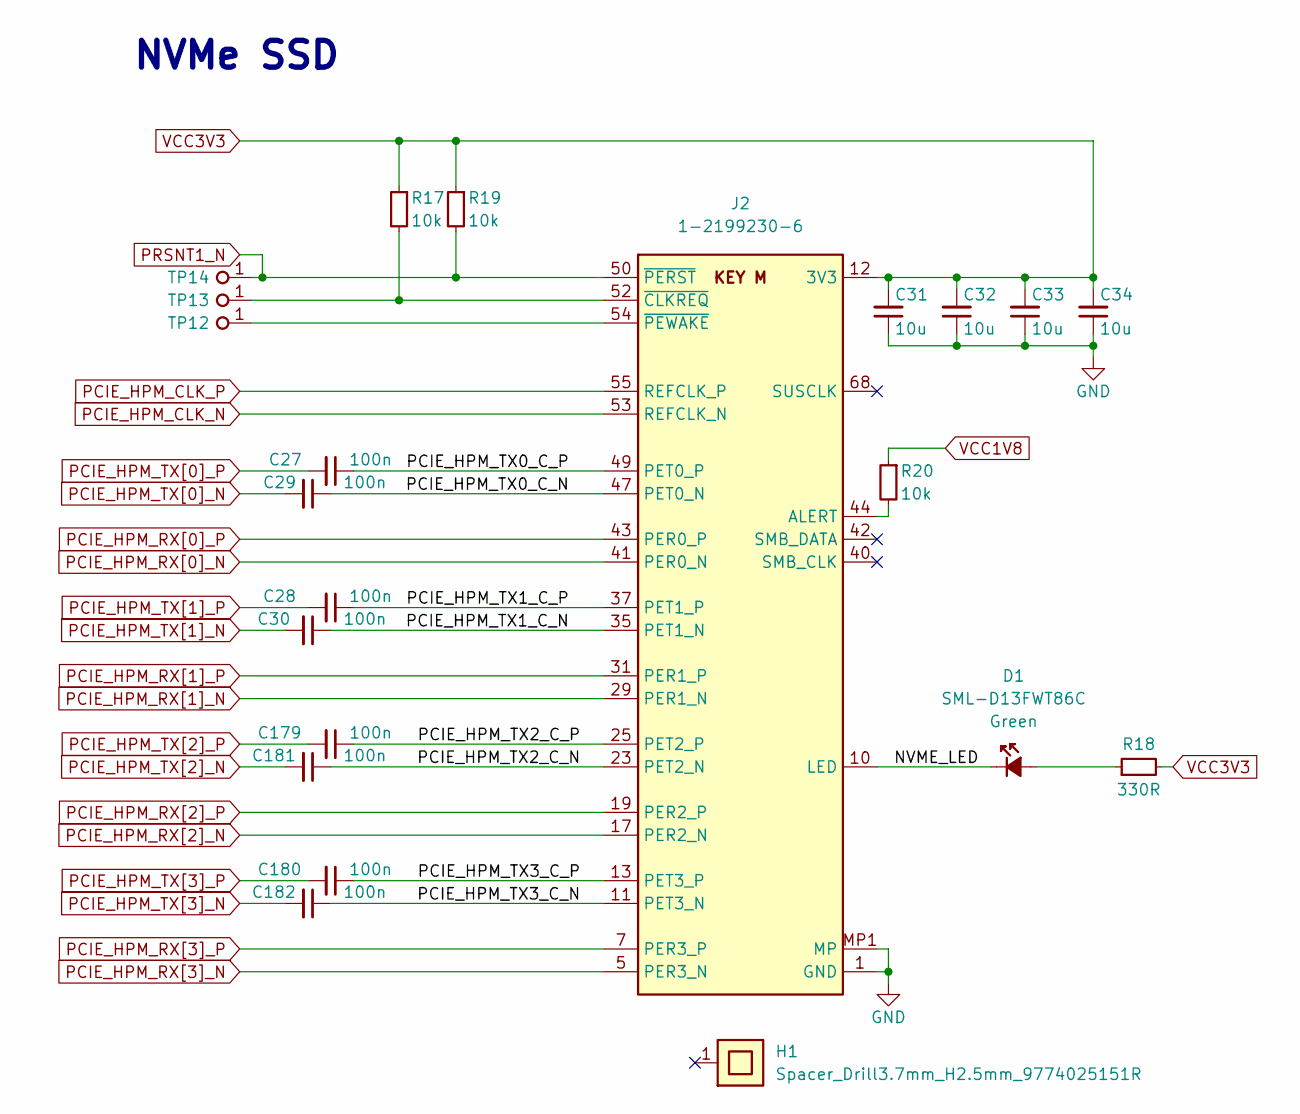
[picture p27: schematic pcie-conn.kicad_sch]

Parts:
C27, C28, C29, C30, C179, C180, C181, C182: C_100n_6V3_0402; C_0402_1005Metric; MPN 0402X104K6R3CT
C31, C32, C33, C34: C_10u_0402; C_0402_1005Metric; MPN CC0402MRX5R5BB106
D1: LED_G_0603_KP-1608CGCK; LED_0603_1608Metric_G; MPN SML-D13FWT86C
H1: Spacer_Drill3.7mm_H2.5mm_9774025151R; MPN 9774025151R
J2: Bus_M.2_1-2199230-6; Bus_M.2_Socket_Key_M_TE_1-2199230-6; MPN 1-2199230-6
R17, R19, R20: R_10k_0402; R_0402_1005Metric; Tolerance 1%; MPN CR0402AFX-1002GAS
R18: R_330R_0402; R_0402_1005Metric; Tolerance 1%; MPN CR0402-FX-3300GLF
TP12, TP13, TP14: TP_1mm_SMD; TP_SMD_1mm

Connections:
GND: C31.1, C32.1, C33.1, C34.1, J2.1 (GND), J2.3 (GND), J2.9 (GND), J2.15 (GND), J2.21 (GND), J2.27 (GND), J2.33 (GND), J2.39 (GND), J2.45 (GND), J2.51 (GND), J2.57 (GND), J2.71 (GND), J2.73 (GND), J2.75 (GND), J2.MP1 (MP), J2.MP2 (MP)
NVME_LED: D1.1 (C), J2.10 (LED)
unnamed: D1.2 (A), R18.1
unnamed: J2.44 (ALERT), R20.2
unnamed: J2.52 (~CLKREQ), R17.2, TP13.1
unnamed: J2.54 (~PEWAKE), TP12.1
PCIE_HPM_CLK_N: J2.53 (REFCLK_N)
PCIE_HPM_CLK_P: J2.55 (REFCLK_P)
PCIE_HPM_RX[0]_N: J2.41 (PER0_N)
PCIE_HPM_RX[0]_P: J2.43 (PER0_P)
PCIE_HPM_RX[1]_N: J2.29 (PER1_N)
PCIE_HPM_RX[1]_P: J2.31 (PER1_P)
PCIE_HPM_RX[2]_N: J2.17 (PER2_N)
PCIE_HPM_RX[2]_P: J2.19 (PER2_P)
PCIE_HPM_RX[3]_N: J2.5 (PER3_N)
PCIE_HPM_RX[3]_P: J2.7 (PER3_P)
PCIE_HPM_TX0_C_N: C29.1, J2.47 (PET0_N)
PCIE_HPM_TX0_C_P: C27.1, J2.49 (PET0_P)
PCIE_HPM_TX1_C_N: C30.1, J2.35 (PET1_N)
PCIE_HPM_TX1_C_P: C28.1, J2.37 (PET1_P)
PCIE_HPM_TX2_C_N: C181.1, J2.23 (PET2_N)
PCIE_HPM_TX2_C_P: C179.1, J2.25 (PET2_P)
PCIE_HPM_TX3_C_N: C182.1, J2.11 (PET3_N)
PCIE_HPM_TX3_C_P: C180.1, J2.13 (PET3_P)
PCIE_HPM_TX[0]_N: C29.2
PCIE_HPM_TX[0]_P: C27.2
PCIE_HPM_TX[1]_N: C30.2
PCIE_HPM_TX[1]_P: C28.2
PCIE_HPM_TX[2]_N: C181.2
PCIE_HPM_TX[2]_P: C179.2
PCIE_HPM_TX[3]_N: C182.2
PCIE_HPM_TX[3]_P: C180.2
PRSNT1_N: J2.50 (~PERST), R19.2, TP14.1
VCC1V8: R20.1
VCC3V3: C31.2, C32.2, C33.2, C34.2, J2.2 (3V3), J2.4 (3V3), J2.12 (3V3), J2.14 (3V3), J2.16 (3V3), J2.18 (3V3), J2.70 (3V3), J2.72 (3V3), J2.74 (3V3), R17.1, R18.2, R19.1

Notes on the sheet:
NVMe SSD
