vollbert/artix-dc-scm/power-supply.kicad_sch

## KiCad design power-supply.kicad_sch (2026-04-19)

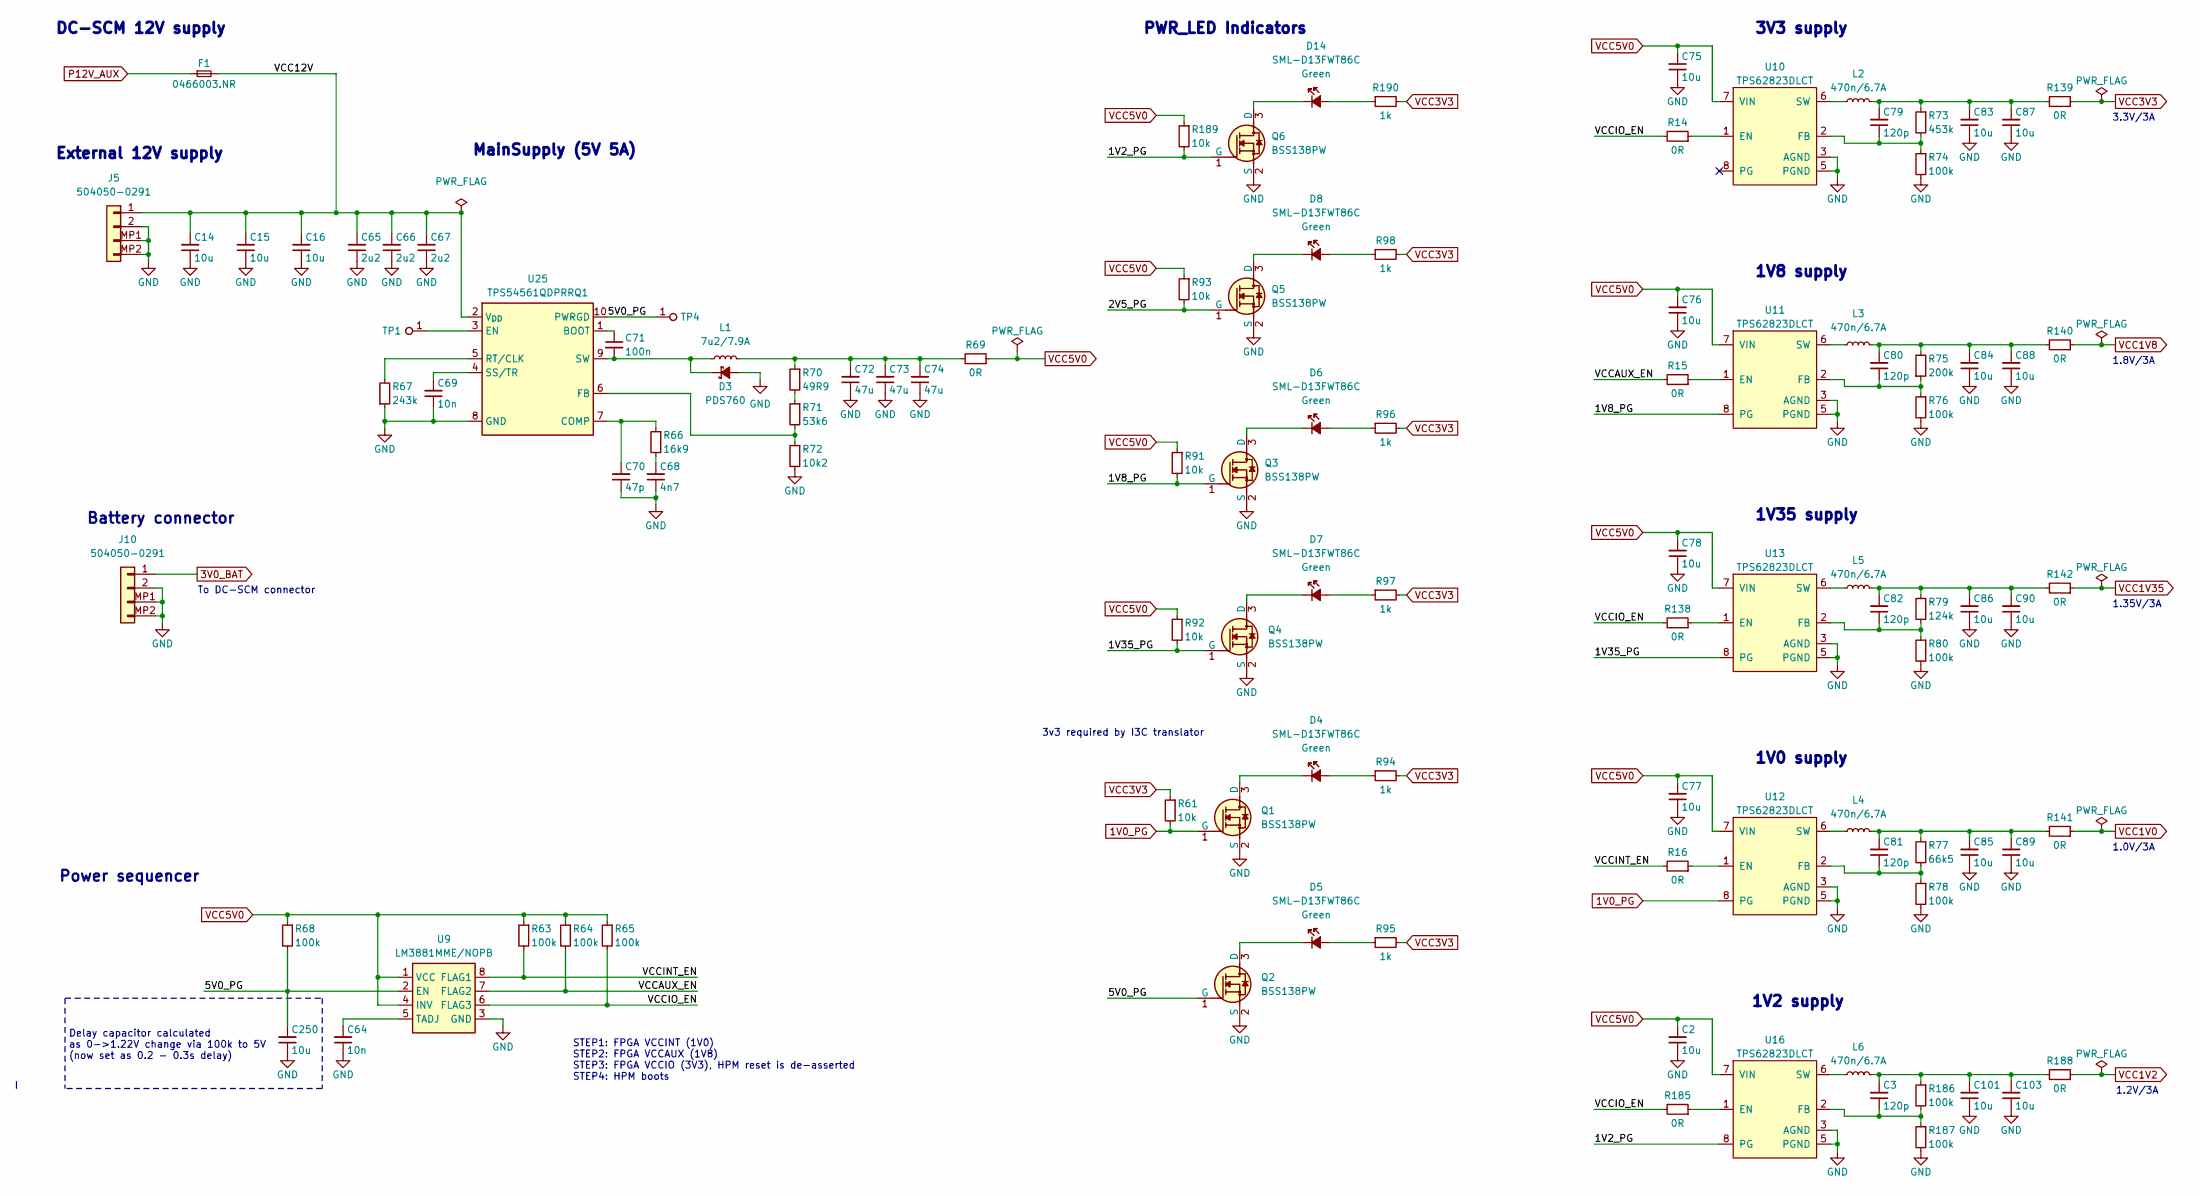
[picture p28: schematic power-supply.kicad_sch]

Parts:
C2, C75, C76, C77, C78: C_10u_0603; C_0603_1608Metric; MPN GRT188R61A106KE13D
C3, C79, C80, C81, C82: C_120p_0402; C_0402_1005Metric; Voltage 100V; MPN C0402C121J5GACTU
C14, C15, C16: C_10u_25V_0603; C_0603_1608Metric; Voltage 25V; MPN C1608X5R1E106M080AC
C64, C69: C_10n_0402; C_0402_1005Metric; Voltage 50V; MPN GRM155R71H103KA88D
C65, C66, C67: C_2u2_0603_25V; C_0603_1608Metric; MPN GRM188R61E225KA12D
C68: C_4n7_0402; C_0402_1005Metric; MPN CC0402KRX7R0BB472
C70: C_47p_0402; C_0402_1005Metric; MPN C0402C470J5GACTU
C71: C_100n_6V3_0402; C_0402_1005Metric; MPN 0402X104K6R3CT
C72, C73, C74: C_47u_0603; C_0603_1608Metric; MPN GRM188R60J476ME15D
C83, C84, C85, C86, C87, C88, C89, C90, C101, C103, C250: C_10u_0402; C_0402_1005Metric; MPN CC0402MRX5R5BB106
D3: PDS760; PowerDI5; MPN PDS760-13
D4, D5, D6, D7, D8, D14: LED_G_0603_LG_L29K-G2J1-24-Z; LED_0603_1608Metric_G; MPN SML-D13FWT86C
F1: F_3A_1206; F_1206_3216Metric; MPN 0466003.NR
J5, J10: Molex_Pico-Lock_1x2_504050-0291; Conn_Molex_Pico-Lock_1x2_504050-0291; MPN 504050-0291
L1: L_7u2_7.9A_WE-PDF-1064; L_WE-PDF-1064; MPN 7447798720
L2, L3, L4, L5, L6: L_470n_6.7A_Vishay-IHLP-1212AE-11; L_Vishay-IHLP-1212AE; MPN IHLP1212AEEZR47M1Z
Q1, Q2, Q3, Q4, Q5, Q6: BSS138PW; SC70-3; MPN BSS138BKW,115
R14, R15, R16, R138, R185: R_0R_0402; R_0402_1005Metric; MPN RC0402JR-7D0RL
R61, R91, R92, R93, R189: R_10k_0402; R_0402_1005Metric; Tolerance 1%; MPN CR0402AFX-1002GAS
R63, R64, R65, R68, R74, R76, R78, R80, R186, R187: R_100k_0402; R_0402_1005Metric; Tolerance 1%; MPN CR0402-FX-1003GLF
R66: R_16k9_0402; R_0402_1005Metric; Tolerance 1%; MPN CR0402-FX-1692GLF
R67: R_243k_0402; R_0402_1005Metric; Tolerance 1%; MPN CR0402-FX-2433GLF
R69: R_0R_1206; R_1206_3216Metric; MPN CRCW12060000Z0EAHP
R70: R_49R9_0402; R_0402_1005Metric; Tolerance 1%; MPN CR0402-FX-49R9GLF
R71: R_53k6_0402; R_0402_1005Metric; Tolerance 1%; MPN CR0402-FX-5362GLF
R72: R_10k2_0402; R_0402_1005Metric; Tolerance 1%; MPN CR0402-FX-1022GLF
R73: R_453k_0402; R_0402_1005Metric; Tolerance 1%; MPN CR0402-FX-4533GLF
R75: R_200k_0402; R_0402_1005Metric; Tolerance 1%; MPN CR0402-FX-2003GLF
R77: R_66k5_0402; R_0402_1005Metric; Tolerance 1%; MPN CR0402-FX-6652GLF
R79: R_124k_0402; R_0402_1005Metric; Tolerance 1%; MPN CR0402-FX-1243GLF
R94, R95, R96, R97, R98, R190: R_1k_0402; R_0402_1005Metric; Tolerance 1%; MPN CR0402-FX-1001GLF
R139, R140, R141, R142, R188: R_0R_0603; R_0603_1608Metric; MPN CR0603-J/-000ELF
TP1, TP4: TP_1mm_SMD; TP_SMD_1mm
U9: LM3881; VSSOP-8_3x3mm_P0.65mm; MPN LM3881MME/NOPB
U10, U11, U12, U13, U16: TPS62823DLCT; QFN-8_2x1.5mm; MPN TPS62823DLCT
U25: TPS54561QDPRRQ1; WSON-10-1EP_4x4mm_P0.8mm_EP2.6x3mm; MPN TPS54561QDPRRQ1

Connections:
1V0_PG: Q1.1 (G), R61.2, U12.8 (PG)
1V2_PG: Q6.1 (G), R189.2, U16.8 (PG)
1V8_PG: Q3.1 (G), R91.2, U11.8 (PG)
1V35_PG: Q4.1 (G), R92.2, U13.8 (PG)
2V5_PG: Q5.1 (G), R93.2
3V0_BAT: J10.1
5V0_PG: C250.2, Q2.1 (G), R68.2, TP4.1, U9.2 (EN), U25.10 (PWRGD)
GND: C2.1, C14.1, C15.1, C16.1, C64.1, C65.1, C66.1, C67.1, C68.1, C69.1, C70.1, C72.1, C73.1, C74.1, C75.1, C76.1, C77.1, C78.1, C83.1, C84.1, C85.1, C86.1, C87.1, C88.1, C89.1, C90.1, C101.1, C103.1, C250.1, D3.2 (A), J5.2, J5.MP1 (MP), J5.MP2, J10.2, J10.MP1 (MP), J10.MP2, Q1.2 (S), Q2.2 (S), Q3.2 (S), Q4.2 (S), Q5.2 (S), Q6.2 (S), R67.1, R72.2, R74.2, R76.2, R78.2, R80.2, R187.2, U9.3 (GND), U10.3 (AGND), U10.5 (PGND), U11.3 (AGND), U11.5 (PGND), U12.3 (AGND), U12.5 (PGND), U13.3 (AGND), U13.5 (PGND), U16.3 (AGND), U16.5 (PGND), U25.8 (GND), U25.11 (GND)
unnamed: C3.1, R186.2, R187.1, U16.2 (FB)
unnamed: C64.2, U9.5 (TADJ)
unnamed: C68.2, R66.2
unnamed: C69.2, U25.4 (SS/TR)
unnamed: C70.2, R66.1, U25.7 (COMP)
unnamed: C71.1, U25.1 (BOOT)
unnamed: C71.2, D3.1 (C), L1.1, U25.9 (SW)
unnamed: C72.2, C73.2, C74.2, L1.2, R69.2, R70.1
unnamed: C79.1, R73.2, R74.1, U10.2 (FB)
unnamed: C79.2, C83.2, C87.2, L2.2, R73.1, R139.2
unnamed: C80.1, R75.1, R76.1, U11.2 (FB)
unnamed: C80.2, C84.2, C88.2, L3.2, R75.2, R140.2
unnamed: C81.1, R77.2, R78.1, U12.2 (FB)
unnamed: C81.2, C85.2, C89.2, L4.2, R77.1, R141.2
unnamed: C82.1, R79.2, R80.1, U13.2 (FB)
unnamed: C82.2, C86.2, C90.2, L5.2, R79.1, R142.2
unnamed: C3.2, C101.2, C103.2, L6.2, R186.1, R188.2
unnamed: D4.1 (C), Q1.3 (D)
unnamed: D4.2 (A), R94.1
unnamed: D5.1 (C), Q2.3 (D)
unnamed: D5.2 (A), R95.1
unnamed: D6.1 (C), Q3.3 (D)
unnamed: D6.2 (A), R96.1
unnamed: D7.1 (C), Q4.3 (D)
unnamed: D7.2 (A), R97.1
unnamed: D8.1 (C), Q5.3 (D)
unnamed: D8.2 (A), R98.1
unnamed: D14.1 (C), Q6.3 (D)
unnamed: D14.2 (A), R190.1
unnamed: L2.1, U10.6 (SW)
unnamed: L3.1, U11.6 (SW)
unnamed: L4.1, U12.6 (SW)
unnamed: L5.1, U13.6 (SW)
unnamed: L6.1, U16.6 (SW)
unnamed: R14.1, U10.1 (EN)
unnamed: R15.1, U11.1 (EN)
unnamed: R16.1, U12.1 (EN)
unnamed: R67.2, U25.5 (RT/CLK)
unnamed: R70.2, R71.1
unnamed: R71.2, R72.1, U25.6 (FB)
unnamed: R138.1, U13.1 (EN)
unnamed: R185.1, U16.1 (EN)
unnamed: TP1.1, U25.3 (EN)
P12V_AUX: F1.1
VCC1V0: R141.1
VCC1V2: R188.1
VCC1V8: R140.1
VCC1V35: R142.1
VCC3V3: R61.1, R94.2, R95.2, R96.2, R97.2, R98.2, R139.1, R190.2
VCC5V0: C2.2, C75.2, C76.2, C77.2, C78.2, R63.1, R64.1, R65.1, R68.1, R69.1, R91.1, R92.1, R93.1, R189.1, U9.1 (VCC), U9.4 (INV), U10.7 (VIN), U11.7 (VIN), U12.7 (VIN), U13.7 (VIN), U16.7 (VIN)
VCC12V: C14.2, C15.2, C16.2, C65.2, C66.2, C67.2, F1.2, J5.1, U25.2 (V_{DD})
VCCAUX_EN: R15.2, R64.2, U9.7 (FLAG2)
VCCINT_EN: R16.2, R63.2, U9.8 (FLAG1)
VCCIO_EN: R14.2, R65.2, R138.2, R185.2, U9.6 (FLAG3)

Notes on the sheet:
1.8V/3A
Delay capacitor calculated as 0->1.22V change via 100k to 5V (now set as 0.2 - 0.3s delay)
3.3V/3A
1.0V/3A
1V8 supply
1V0 supply
1.35V/3A
1V2 supply
To DC-SCM connector
3v3 required by I3C translator
STEP1: FPGA VCCINT (1V0) STEP2: FPGA VCCAUX (1V8) STEP3: FPGA VCCIO (3V3), HPM reset is de-asserted STEP4: HPM boots
DC-SCM 12V supply
Power sequencer
MainSupply (5V 5A)
1V35 supply
PWR_LED Indicators
3V3 supply
1.2V/3A
Battery connector
External 12V supply
