vollbert/artix-dc-scm/rot.kicad_sch

## KiCad design rot.kicad_sch (2026-04-19)

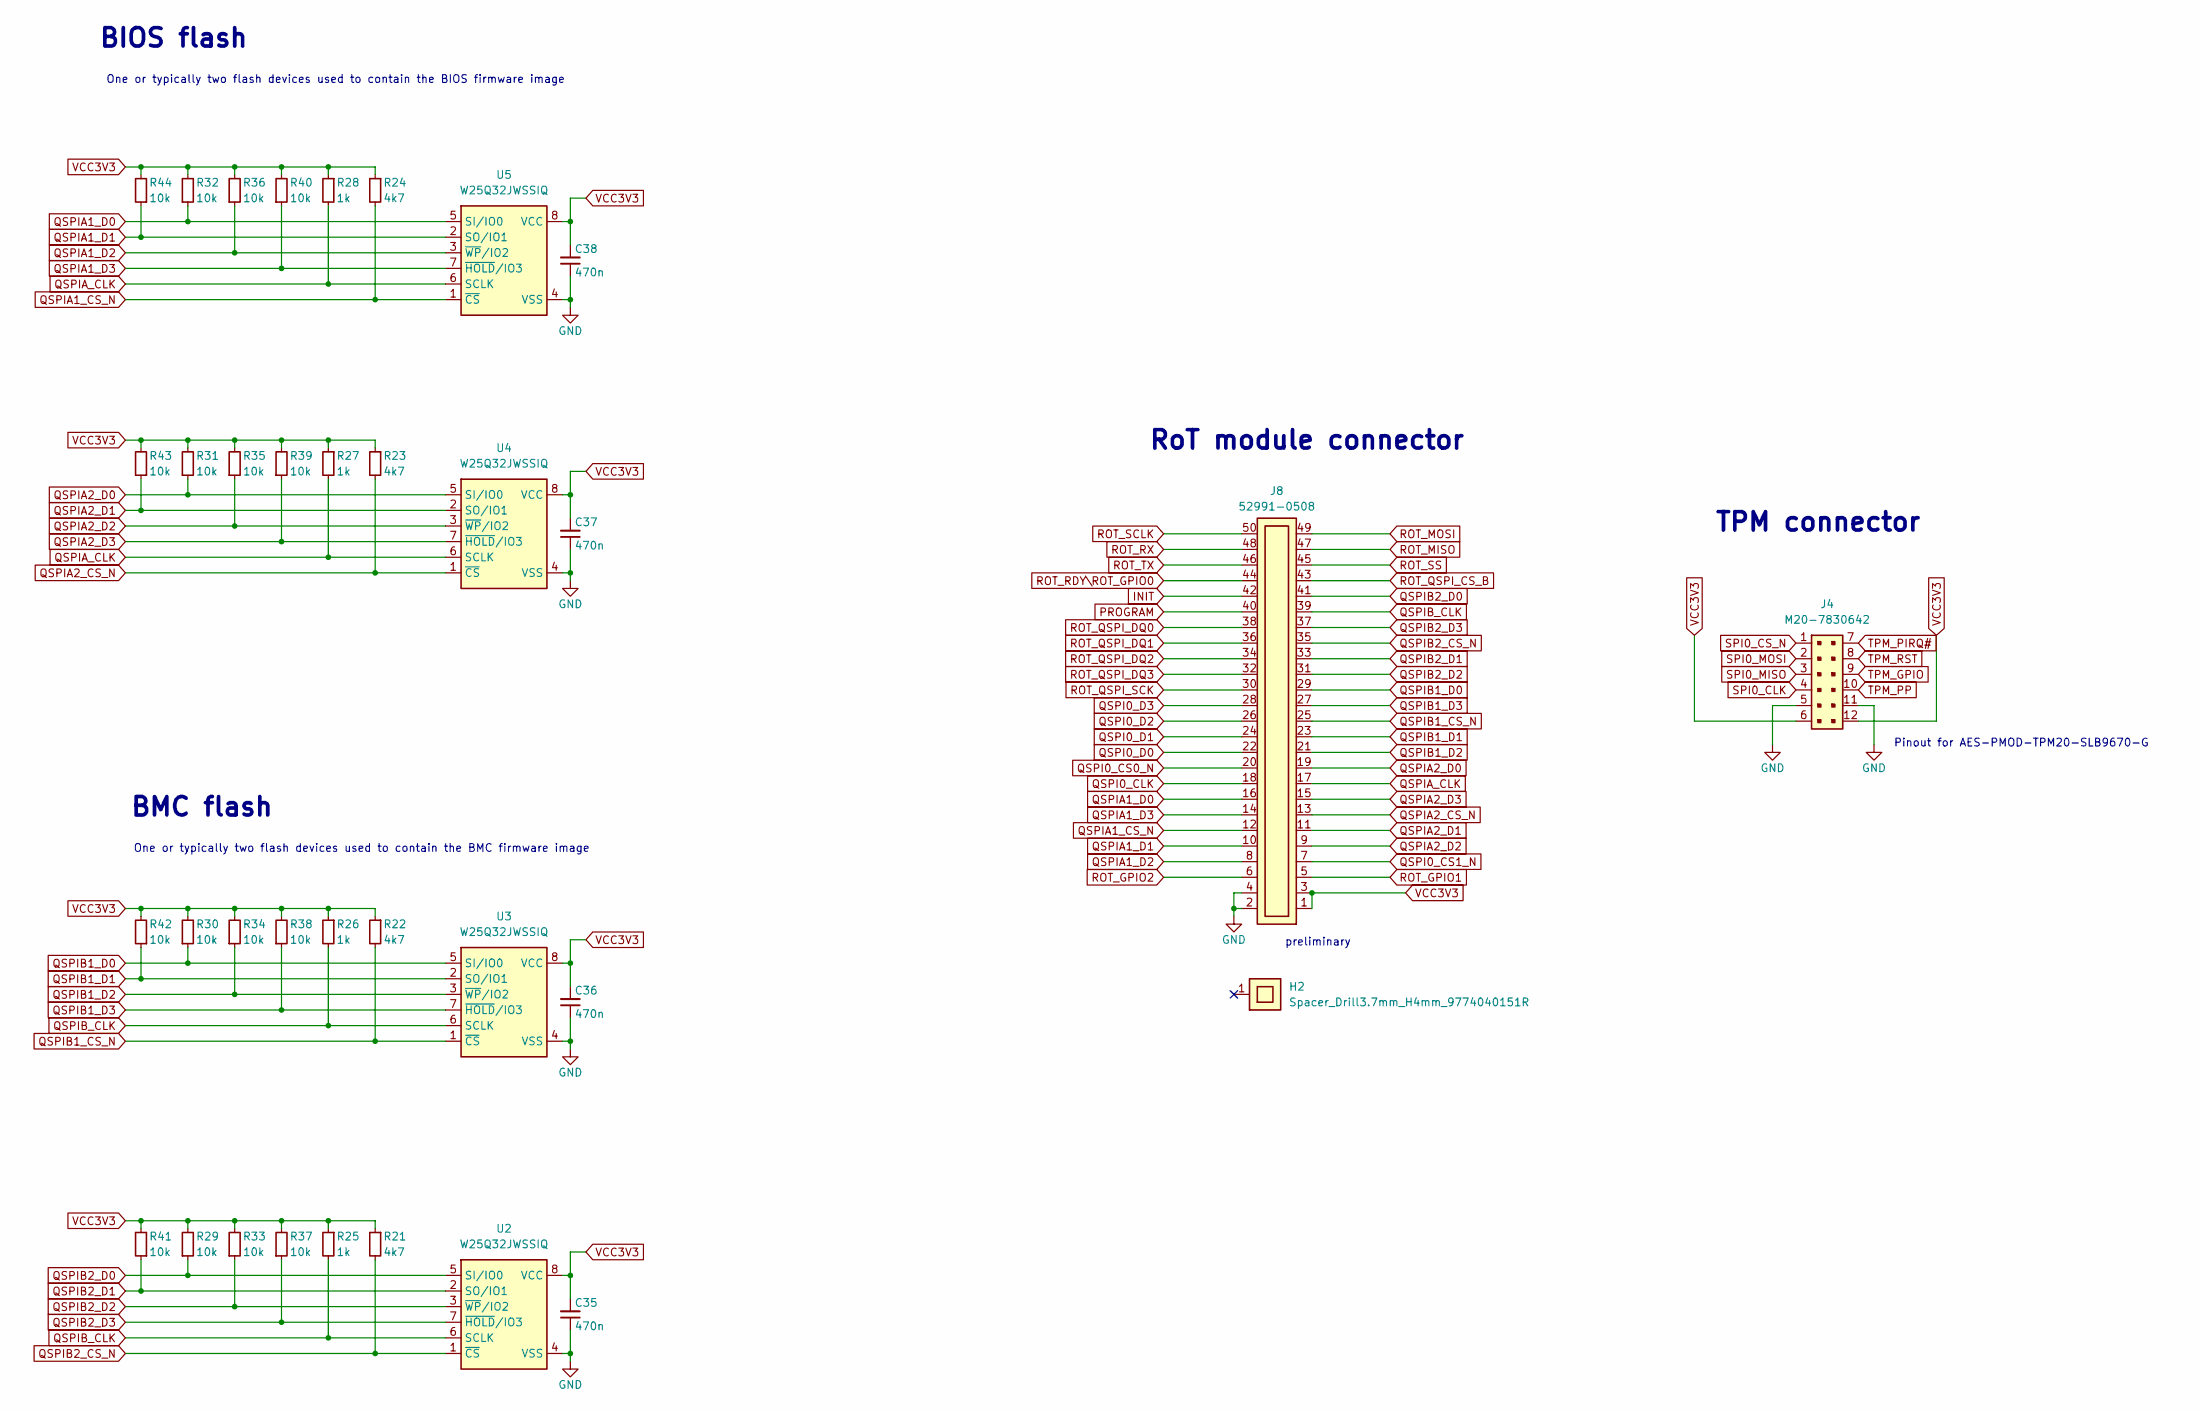
[picture p29: schematic rot.kicad_sch]

Parts:
C35, C36, C37, C38: C_470n_0402; C_0402_1005Metric; MPN GXT155C80J474KE01D
H2: Spacer_Drill3.7mm_H4mm_9774040151R; MPN 9774040151R
J4: PinSocket_2x6_P2.54mm_Drill1.02mm_PMOD; MPN M20-7830642
J8: Plug_Molex_SlimStack_2x25_529910508; Conn_Plug_Molex_SlimStack_2x25_529910508; MPN 52991-0508
R21, R22, R23, R24: R_4k7_0402; R_0402_1005Metric; Tolerance 1%; MPN RC0402FR-7D4K7L
R25, R26, R27, R28: R_1k_0402; R_0402_1005Metric; Tolerance 1%; MPN CR0402-FX-1001GLF
R29, R30, R31, R32, R33, R34, R35, R36, R37, R38, R39, R40, R41, R42, R43, R44: R_10k_0402; R_0402_1005Metric; Tolerance 1%; MPN CR0402AFX-1002GAS
U2, U3, U4, U5: W25Q32JW_SOIC-8; SOIC-8_5.3x5.3x2mm_P1.27mm; MPN W25Q32JWSSIQ

Connections:
GND: C35.1, C36.1, C37.1, C38.1, J4.5, J4.11, J8.2, J8.4, U2.4 (VSS), U3.4 (VSS), U4.4 (VSS), U5.4 (VSS)
INIT: J8.42
PROGRAM: J8.40
QSPI0_CLK: J8.18
QSPI0_CS0_N: J8.20
QSPI0_CS1_N: J8.7
QSPI0_D0: J8.22
QSPI0_D1: J8.24
QSPI0_D2: J8.26
QSPI0_D3: J8.28
QSPIA1_CS_N: J8.12, R24.2, U5.1 (~CS)
QSPIA1_D0: J8.16, R32.1, U5.5 (SI/IO0)
QSPIA1_D1: J8.10, R44.1, U5.2 (SO/IO1)
QSPIA1_D2: J8.8, R36.1, U5.3 (~WP/IO2)
QSPIA1_D3: J8.14, R40.1, U5.7 (~HOLD/IO3)
QSPIA2_CS_N: J8.13, R23.2, U4.1 (~CS)
QSPIA2_D0: J8.19, R31.1, U4.5 (SI/IO0)
QSPIA2_D1: J8.11, R43.1, U4.2 (SO/IO1)
QSPIA2_D2: J8.9, R35.1, U4.3 (~WP/IO2)
QSPIA2_D3: J8.15, R39.1, U4.7 (~HOLD/IO3)
QSPIA_CLK: J8.17, R27.2, R28.2, U4.6 (SCLK), U5.6 (SCLK)
QSPIB1_CS_N: J8.25, R22.2, U3.1 (~CS)
QSPIB1_D0: J8.29, R30.1, U3.5 (SI/IO0)
QSPIB1_D1: J8.23, R42.1, U3.2 (SO/IO1)
QSPIB1_D2: J8.21, R34.1, U3.3 (~WP/IO2)
QSPIB1_D3: J8.27, R38.1, U3.7 (~HOLD/IO3)
QSPIB2_CS_N: J8.35, R21.2, U2.1 (~CS)
QSPIB2_D0: J8.41, R29.1, U2.5 (SI/IO0)
QSPIB2_D1: J8.33, R41.1, U2.2 (SO/IO1)
QSPIB2_D2: J8.31, R33.1, U2.3 (~WP/IO2)
QSPIB2_D3: J8.37, R37.1, U2.7 (~HOLD/IO3)
QSPIB_CLK: J8.39, R25.2, R26.2, U2.6 (SCLK), U3.6 (SCLK)
ROT_GPIO1: J8.5
ROT_GPIO2: J8.6
ROT_MISO: J8.47
ROT_MOSI: J8.49
ROT_QSPI_CS_B: J8.43
ROT_QSPI_DQ0: J8.38
ROT_QSPI_DQ1: J8.36
ROT_QSPI_DQ2: J8.34
ROT_QSPI_DQ3: J8.32
ROT_QSPI_SCK: J8.30
ROT_RDY\ROT_GPIO0: J8.44
ROT_RX: J8.48
ROT_SCLK: J8.50
ROT_SS: J8.45
ROT_TX: J8.46
SPI0_CLK: J4.4
SPI0_CS_N: J4.1
SPI0_MISO: J4.3
SPI0_MOSI: J4.2
TPM_GPIO: J4.9
TPM_PIRQ#: J4.7
TPM_PP: J4.10
TPM_RST: J4.8
VCC3V3: C35.2, C36.2, C37.2, C38.2, J4.6, J4.12, J8.1, J8.3, R21.1, R22.1, R23.1, R24.1, R25.1, R26.1, R27.1, R28.1, R29.2, R30.2, R31.2, R32.2, R33.2, R34.2, R35.2, R36.2, R37.2, R38.2, R39.2, R40.2, R41.2, R42.2, R43.2, R44.2, U2.8 (VCC), U3.8 (VCC), U4.8 (VCC), U5.8 (VCC)

Notes on the sheet:
RoT module connector
One or typically two flash devices used to contain the BMC firmware image
TPM connector
BMC flash
BIOS flash
One or typically two flash devices used to contain the BIOS firmware image
Pinout for AES-PMOD-TPM20-SLB9670-G
preliminary
